studio8502/Sentinel-65X/kicad/Sentinel 65X - Prototype 3 Mini/Sentinel 65X - Prototype 3 Mini.kicad_sch

## KiCad design kicad/Sentinel 65X - Prototype 3 Mini/Sentinel 65X - Prototype 3 Mini.kicad_sch (2024-02-07)

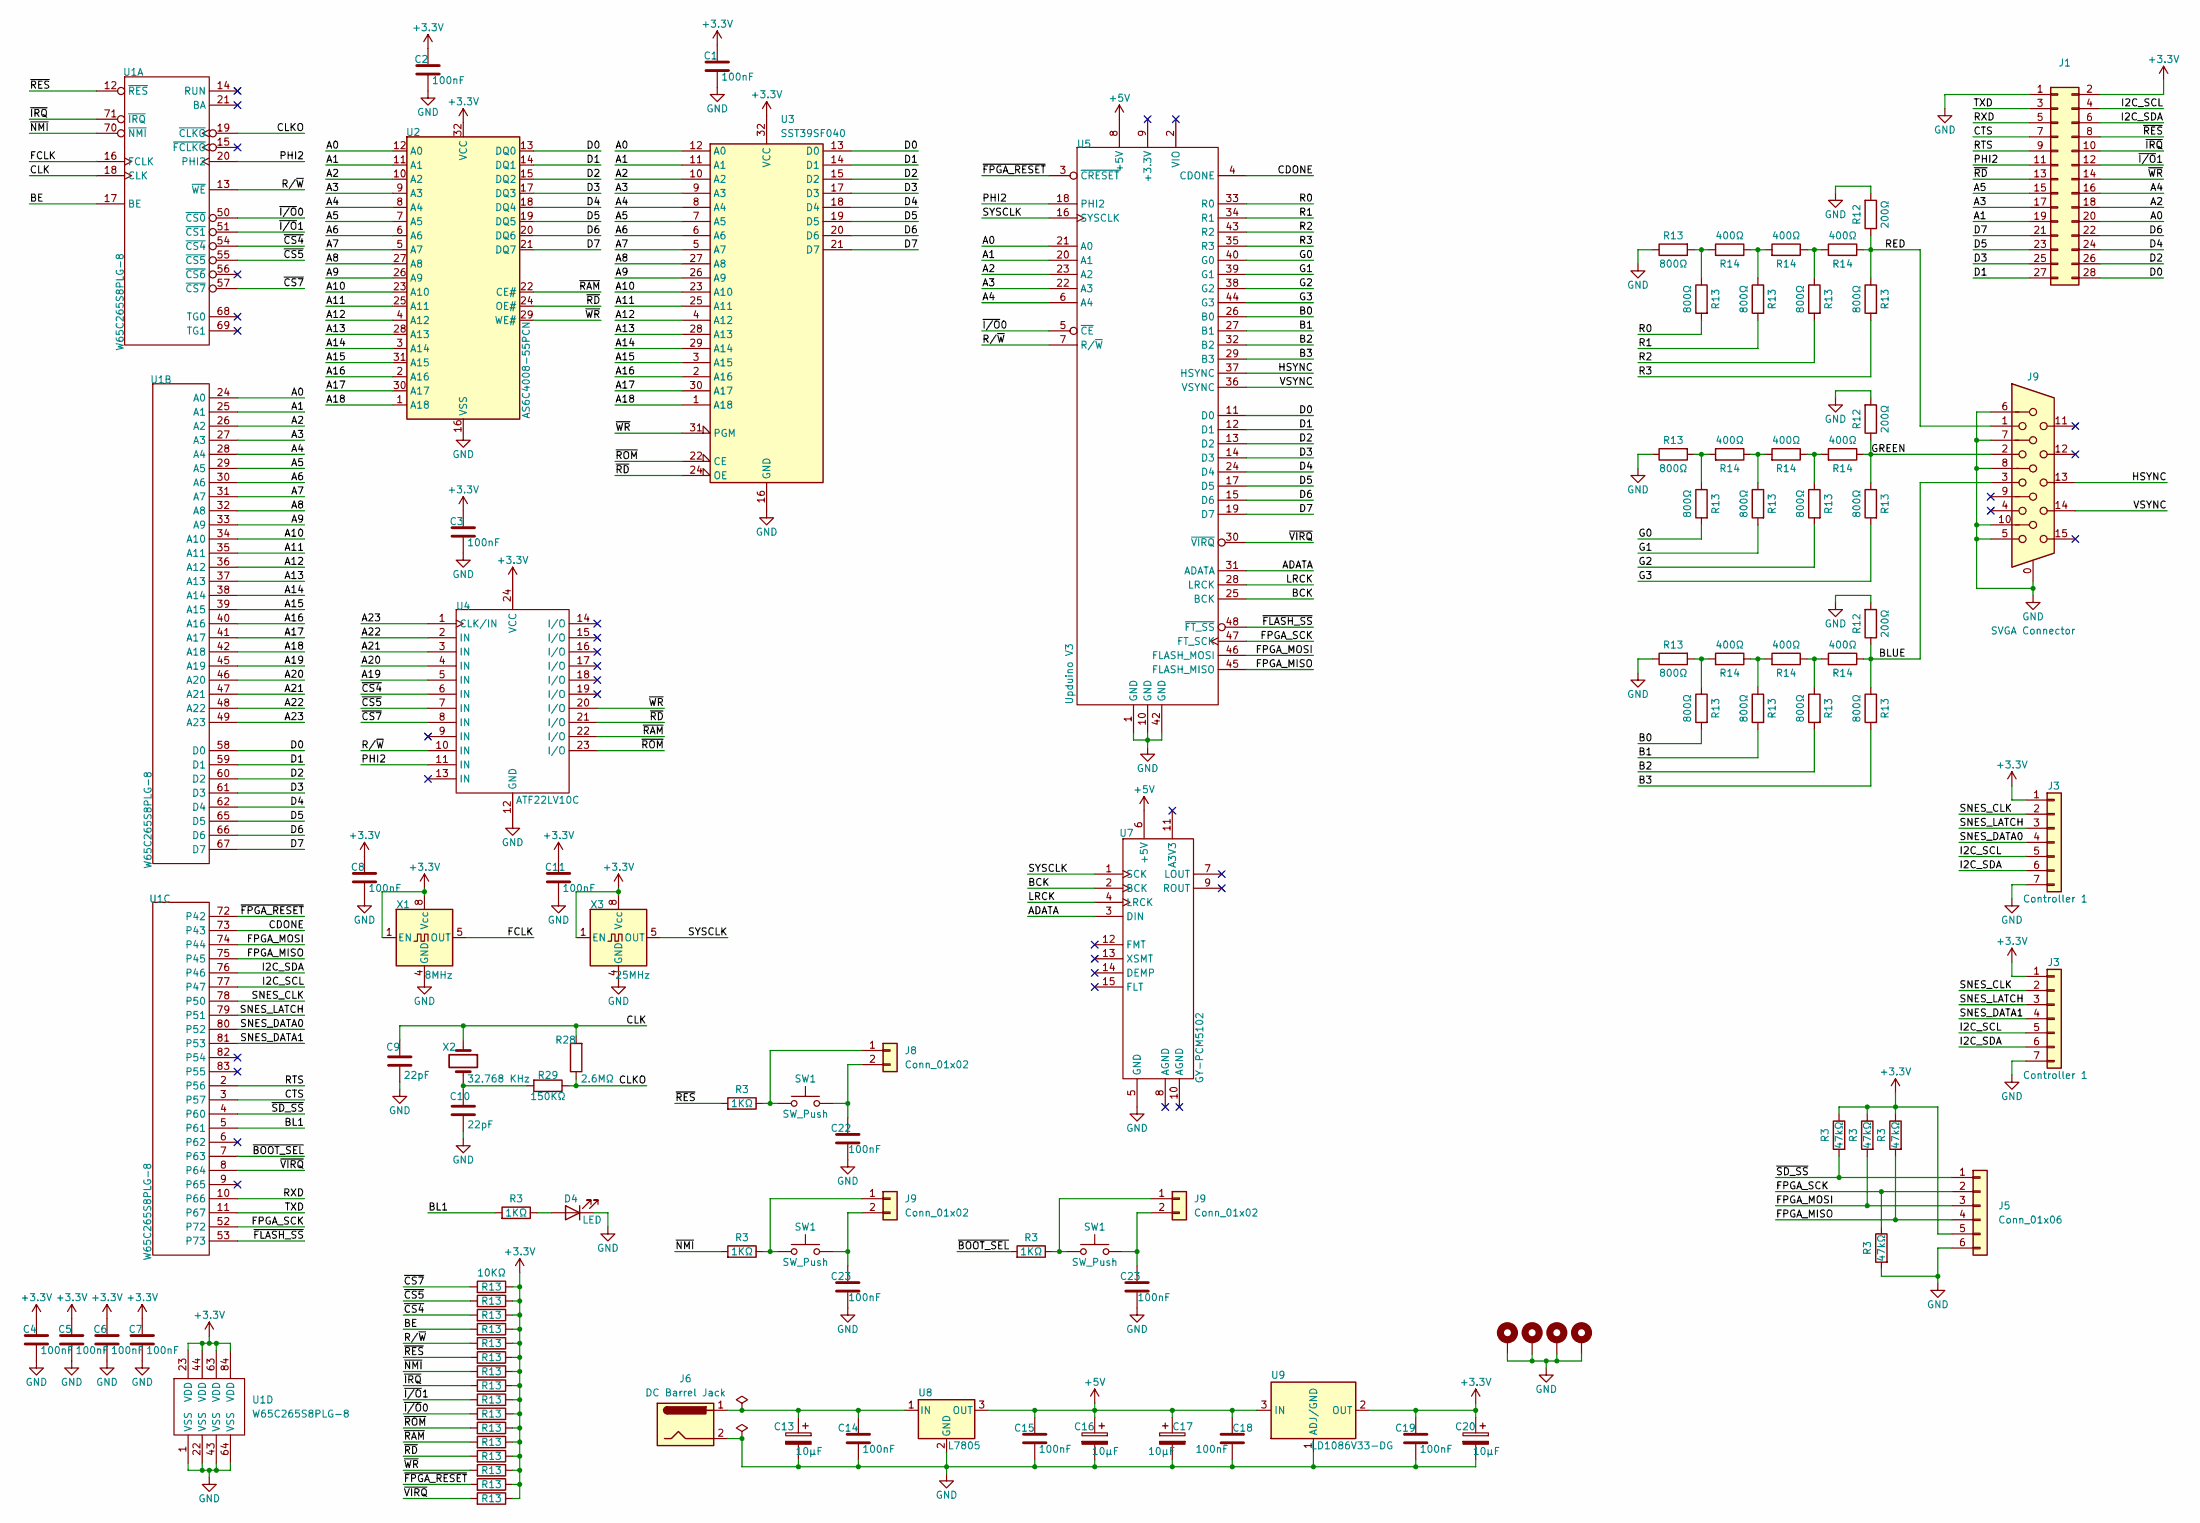
[picture p14: schematic Sentinel 65X - Prototype 3 Mini.kicad_sch]

Parts:
C1, C2, C3, C4, C5, C6, C7, C8, C11, C14, C15, C18, C19, C22, C23: 100nF; C_Disc_D3.4mm_W2.1mm_P2.50mm
C9, C10: 22pF; C_Disc_D3.0mm_W1.6mm_P2.50mm
C13, C16, C17, C20: 10µF; CP_Radial_D5.0mm_P2.50mm
D4: LED; LED_D3.0mm
H1, H2, H3, H4: MountingHole_Pad; MountingHole_3.2mm_M3_DIN965_Pad
J1: Conn_02x14_Odd_Even; PinSocket_2x14_P2.54mm_Vertical
J3: Controller 1; SNES Controller Port (Female, 90º, THT)
J5: Conn_01x06; PinSocket_1x06_P2.54mm_Horizontal
J6: DC Barrel Jack; BarrelJack_Horizontal
J8: Conn_01x02; PinHeader_1x02_P2.54mm_Vertical
J9: SVGA Connector; DSUB-15-HD_Female_Horizontal_P2.29x1.98mm_EdgePinOffset3.03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
R3: 1KΩ; R_Axial_DIN0204_L3.6mm_D1.6mm_P5.08mm_Horizontal
R12: 200Ω; R_Axial_DIN0204_L3.6mm_D1.6mm_P5.08mm_Horizontal
R13: 10KΩ; R_Axial_DIN0204_L3.6mm_D1.6mm_P5.08mm_Horizontal
R14: 400Ω; R_Axial_DIN0204_L3.6mm_D1.6mm_P5.08mm_Horizontal
R28: 2.6MΩ; R_Axial_DIN0204_L3.6mm_D1.6mm_P5.08mm_Horizontal
R29: 150KΩ; R_Axial_DIN0204_L3.6mm_D1.6mm_P5.08mm_Horizontal
SW1: SW_Push; SW_Tactile_Straight_KSA0Axx1LFTR
U1: W65C265S8PLG-8; PLCC-84_THT-Socket
U2: AS6C4008-55PCN; DIP-32_W15.24mm_Socket_LongPads
U3: SST39SF040; DIP-32_W15.24mm_Socket_LongPads
U4: ATF22LV10C; DIP-24_W7.62mm_Socket_LongPads
U5: Upduino V3; DIP-48_W17.76mm_Socket_LongPads
U7: GY-PCM5102
U8: L7805; TO-220-3_Vertical
U9: LD1086V33-DG; TO-220-3_Vertical
X1: 8MHz; Oscillator_DIP-8
X2: 32.768 KHz; Crystal_DS10_D1.0mm_L4.3mm_Horizontal
X3: 25MHz; Oscillator_DIP-8

Connections:
+3.3V: C1.1, C2.1, C3.1, C4.1, C5.1, C6.1, C7.1, C8.1, C11.1, C19.1, C20.1, J1.2, J3.1, J5.5, R3.1, R13.1, U1.23 (VDD), U1.44 (VDD), U1.63 (VDD), U1.84 (VDD), U2.32 (VCC), U3.32 (VCC), U4.24 (VCC), U9.2 (OUT), X1.1 (EN), X1.8 (Vcc), X3.1 (EN), X3.8 (Vcc)
+5V: C15.1, C16.1, C17.1, C18.1, U5.8 (+5V), U7.6 (+5V), U8.3 (OUT), U9.3 (IN)
A0: J1.20, U1.24 (A0), U2.12 (A0), U3.12 (A0), U5.21 (A0)
A1: J1.19, U1.25 (A1), U2.11 (A1), U3.11 (A1), U5.20 (A1)
A2: J1.18, U1.26 (A2), U2.10 (A2), U3.10 (A2), U5.23 (A2)
A3: J1.17, U1.27 (A3), U2.9 (A3), U3.9 (A3), U5.22 (A3)
A4: J1.16, U1.28 (A4), U2.8 (A4), U3.8 (A4), U5.6 (A4)
A5: J1.15, U1.29 (A5), U2.7 (A5), U3.7 (A5)
A6: U1.30 (A6), U2.6 (A6), U3.6 (A6)
A7: U1.31 (A7), U2.5 (A7), U3.5 (A7)
A8: U1.32 (A8), U2.27 (A8), U3.27 (A8)
A9: U1.33 (A9), U2.26 (A9), U3.26 (A9)
A10: U1.34 (A10), U2.23 (A10), U3.23 (A10)
A11: U1.35 (A11), U2.25 (A11), U3.25 (A11)
A12: U1.36 (A12), U2.4 (A12), U3.4 (A12)
A13: U1.37 (A13), U2.28 (A13), U3.28 (A13)
A14: U1.38 (A14), U2.3 (A14), U3.29 (A14)
A15: U1.39 (A15), U2.31 (A15), U3.3 (A15)
A16: U1.40 (A16), U2.2 (A16), U3.2 (A16)
A17: U1.41 (A17), U2.30 (A17), U3.30 (A17)
A18: U1.42 (A18), U2.1 (A18), U3.1 (A18)
A19: U1.45 (A19), U4.5 (IN)
A20: U1.46 (A20), U4.4 (IN)
A21: U1.47 (A21), U4.3 (IN)
A22: U1.48 (A22), U4.2 (IN)
A23: U1.49 (A23), U4.1 (CLK/IN)
ADATA: U5.31 (ADATA), U7.3 (DIN)
B0: R13.2, U5.26 (B0)
B1: R13.2, U5.27 (B1)
B2: R13.2, U5.32 (B2)
B3: R13.2, U5.29 (B3)
BCK: U5.25 (BCK), U7.2 (BCK)
BE: R13.2, U1.17 (BE)
BL1: R3.2, U1.5 (P61)
BLUE: J9.3, R12.1, R13.1, R14.1
CDONE: U1.73 (P43), U5.4 (CDONE)
CLK: C9.1, R28.2, U1.18 (CLK), X2.1
CLKO: R28.1, R29.1, U1.19 (~CLKO)
CTS: J1.7, U1.3 (P57)
D0: J1.28, U1.58 (D0), U2.13 (DQ0), U3.13 (D0), U5.11 (D0)
D1: J1.27, U1.59 (D1), U2.14 (DQ1), U3.14 (D1), U5.12 (D1)
D2: J1.26, U1.60 (D2), U2.15 (DQ2), U3.15 (D2), U5.13 (D2)
D3: J1.25, U1.61 (D3), U2.17 (DQ3), U3.17 (D3), U5.14 (D3)
D4: J1.24, U1.62 (D4), U2.18 (DQ4), U3.18 (D4), U5.24 (D4)
D5: J1.23, U1.65 (D5), U2.19 (DQ5), U3.19 (D5), U5.17 (D5)
D6: J1.22, U1.66 (D6), U2.20 (DQ6), U3.20 (D6), U5.15 (D6)
D7: J1.21, U1.67 (D7), U2.21 (DQ7), U3.21 (D7), U5.19 (D7)
FCLK: U1.16 (FCLK), X1.5 (OUT)
FPGA_MISO: J5.4, R3.2, U1.75 (P45), U5.45 (FLASH_MISO)
FPGA_MOSI: J5.3, R3.2, U1.74 (P44), U5.46 (FLASH_MOSI)
FPGA_SCK: J5.2, R3.1, U1.52 (P72), U5.47 (FT_SCK)
G0: R13.2, U5.40 (G0)
G1: R13.2, U5.39 (G1)
G2: R13.2, U5.38 (G2)
G3: R13.2, U5.44 (G3)
GND: C1.2, C2.2, C3.2, C4.2, C5.2, C6.2, C7.2, C8.2, C9.2, C10.2, C11.2, C13.2, C14.2, C15.2, C16.2, C17.2, C18.2, C19.2, C20.2, C22.2, C23.2, D4.1 (K), H1.1, H2.1, H3.1, H4.1, J1.1, J3.7, J5.6, J6.2, J9.0, J9.5, J9.6, J9.7, J9.8, J9.10, R3.2, R12.2, R13.1, U1.1 (VSS), U1.22 (VSS), U1.43 (VSS), U1.64 (VSS), U2.16 (VSS), U3.16 (GND), U4.12 (GND), U5.1 (GND), U5.10 (GND), U5.42 (GND), U7.5 (GND), U8.2 (GND), U9.1 (ADJ/GND), X1.4 (GND), X3.4 (GND)
GREEN: J9.2, R12.1, R13.1, R14.1
HSYNC: J9.13, U5.37 (HSYNC)
I2C_SCL: J1.4, J3.5, U1.77 (P47)
I2C_SDA: J1.6, J3.6, U1.76 (P46)
LRCK: U5.28 (LRCK), U7.4 (LRCK)
unnamed: C10.1, R29.2, X2.2
unnamed: C13.1, C14.1, J6.1, U8.1 (IN)
unnamed: C22.1, J8.2, SW1.2
unnamed: C23.1, J9.2, SW1.2
unnamed: D4.2 (A), R3.1
unnamed: J8.1, R3.1, SW1.1
unnamed: J9.1, R3.1, SW1.1
unnamed: R13.1, R13.2, R14.1, R14.2
PHI2: J1.11, U1.20 (PHI2), U4.11 (IN), U5.18 (PHI2)
R0: R13.2, U5.33 (R0)
R1: R13.2, U5.34 (R1)
R2: R13.2, U5.43 (R2)
R3: R13.2, U5.35 (R3)
RED: J9.1, R12.1, R13.1, R14.1
RTS: J1.9, U1.2 (P56)
RXD: J1.5, U1.10 (P66)
R/~W: R13.2, U1.13 (~WE), U4.10 (IN), U5.7 (R/~W)
SNES_CLK: J3.2, U1.78 (P50)
SNES_DATA0: J3.4, U1.80 (P52)
SNES_DATA1: J3.4, U1.81 (P53)
SNES_LATCH: J3.3, U1.79 (P51)
SYSCLK: U5.16 (SYSCLK), U7.1 (SCK), X3.5 (OUT)
TXD: J1.3, U1.11 (P67)
VSYNC: J9.14, U5.36 (VSYNC)
~BOOT_SEL: R3.2, U1.7 (P63)
~CS4: R13.2, U1.54 (~CS4), U4.6 (IN)
~CS5: R13.2, U1.55 (~CS5), U4.7 (IN)
~CS7: R13.2, U1.57 (~CS7), U4.8 (IN)
~FLASH_SS: U1.53 (P73), U5.48 (~FT_SS)
~FPGA_RESET: R13.2, U1.72 (P42), U5.3 (~CRESET)
~IRQ: J1.10, R13.2, U1.71 (~IRQ)
~I/O0: R13.2, U1.50 (~CS0), U5.5 (~CE)
~I/O1: J1.12, R13.2, U1.51 (~CS1)
~NMI: R3.2, R13.2, U1.70 (~NMI)
~RAM: R13.2, U2.22 (CE#), U4.22 (I/O)
~RD: J1.13, R13.2, U2.24 (OE#), U3.24 (OE), U4.21 (I/O)
~RES: J1.8, R3.2, R13.2, U1.12 (~RES)
~ROM: R13.2, U3.22 (CE), U4.23 (I/O)
~SD_SS: J5.1, R3.2, U1.4 (P60)
~VIRQ: R13.2, U1.8 (P64), U5.30 (~VIRQ)
~WR: J1.14, R13.2, U2.29 (WE#), U3.31 (PGM), U4.20 (I/O)
