studio8502/Sentinel-65X/kicad/Sentinel 65X - Prototype 4 V2/AV Port.kicad_sch

## KiCad design kicad/Sentinel 65X - Prototype 4 V2/AV Port.kicad_sch (2024-03-17)

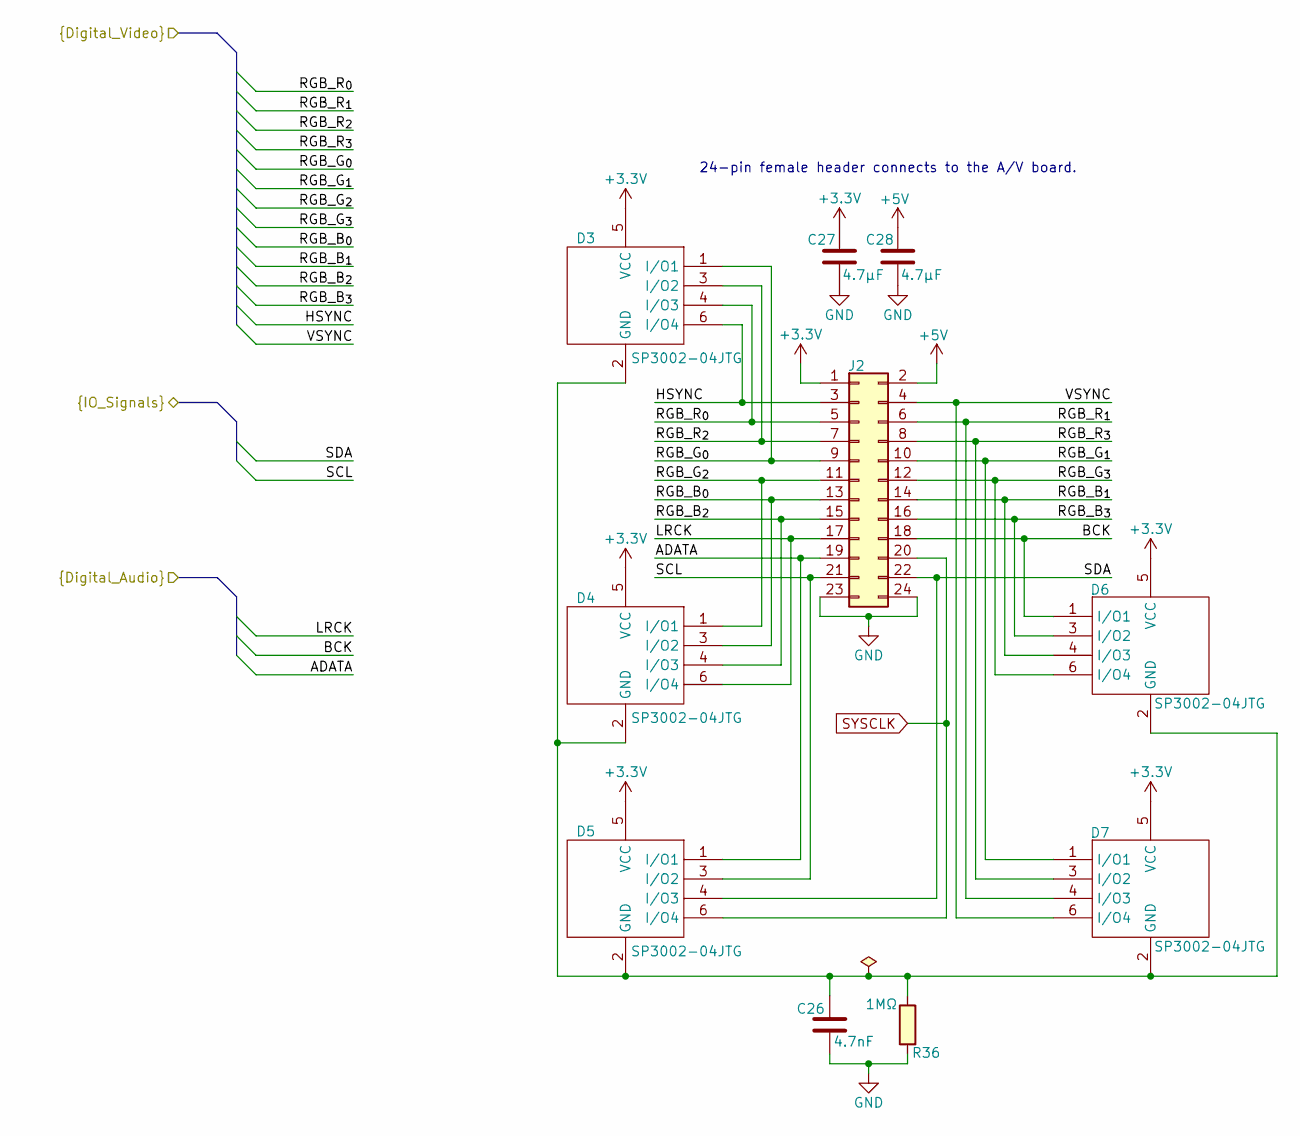
[picture p15: schematic AV Port.kicad_sch]

Parts:
C26: 4.7nF; C_0402_1005Metric
C27, C28: 4.7µF; C_0402_1005Metric
D3, D4, D5, D6, D7: SP3002-04JTG; SOT-363_SC-70-6
J2: Conn_02x12_Odd_Even; PinSocket_2x12_P2.54mm_Vertical
R36: 1MΩ; R_0402_1005Metric

Connections:
+3.3V: C27.1, D3.5 (VCC), D4.5 (VCC), D5.5 (VCC), D6.5 (VCC), D7.5 (VCC), J2.1
+5V: C28.1, J2.2
ADATA: D5.1 (I/O1), J2.19
BCK: D6.1 (I/O1), J2.18
GND: C26.1, C27.2, C28.2, J2.23, J2.24, R36.1
HSYNC: D3.6 (I/O4), J2.3
LRCK: D4.6 (I/O4), J2.17
unnamed: C26.2, D3.2 (GND), D4.2 (GND), D5.2 (GND), D6.2 (GND), D7.2 (GND), R36.2
RGB_B_{0}: D4.3 (I/O2), J2.13
RGB_B_{1}: D6.4 (I/O3), J2.14
RGB_B_{2}: D4.4 (I/O3), J2.15
RGB_B_{3}: D6.3 (I/O2), J2.16
RGB_G_{0}: D3.1 (I/O1), J2.9
RGB_G_{1}: D7.1 (I/O1), J2.10
RGB_G_{2}: D4.1 (I/O1), J2.11
RGB_G_{3}: D6.6 (I/O4), J2.12
RGB_R_{0}: D3.4 (I/O3), J2.5
RGB_R_{1}: D7.4 (I/O3), J2.6
RGB_R_{2}: D3.3 (I/O2), J2.7
RGB_R_{3}: D7.3 (I/O2), J2.8
SCL: D5.3 (I/O2), J2.21
SDA: D5.4 (I/O3), J2.22
SYSCLK: D5.6 (I/O4), J2.20
VSYNC: D7.6 (I/O4), J2.4

Notes on the sheet:
24-pin female header connects to the A/V board.
