studio8502/Sentinel-65X/kicad/Sentinel 65X - Prototype 4 V2/Cartridge Port.kicad_sch

## KiCad design kicad/Sentinel 65X - Prototype 4 V2/Cartridge Port.kicad_sch (2024-03-17)

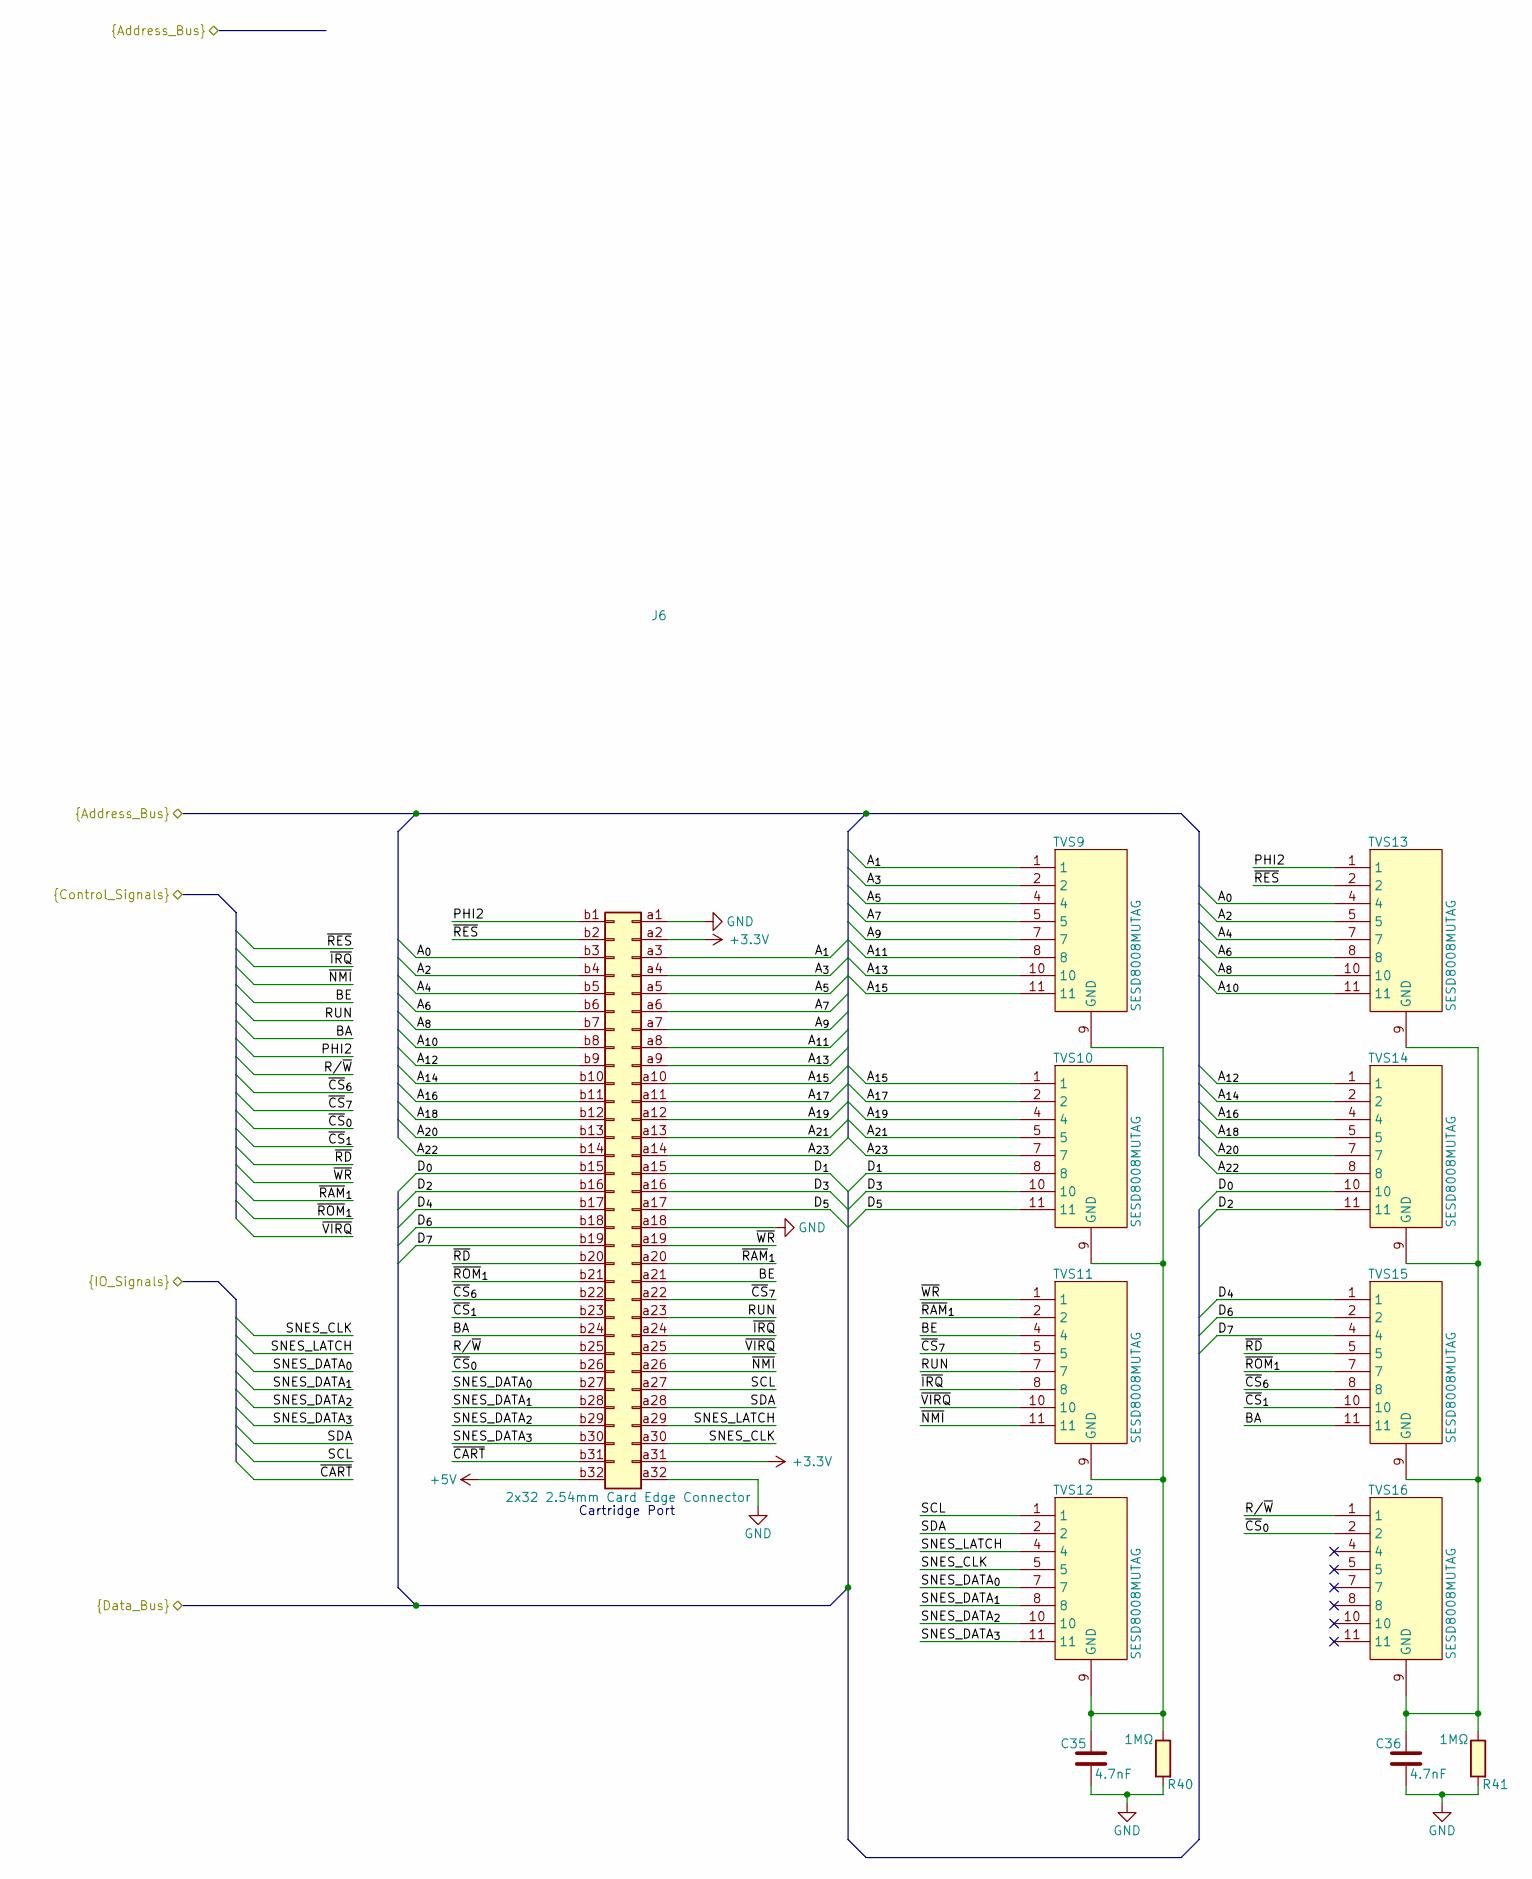
[picture p16: schematic Cartridge Port.kicad_sch]

Parts:
C35, C36: 4.7nF; C_0402_1005Metric
J6: 2x32 2.54mm Card Edge Connector; Sentinel 65X Cartridge Port
R40, R41: 1MΩ; R_0402_1005Metric
TVS9, TVS10, TVS11, TVS12, TVS13, TVS14, TVS15, TVS16: SESD8008MUTAG

Connections:
+3.3V: J6.a2, J6.a31
+5V: J6.b32
A_{0}: J6.b3, TVS13.4
A_{1}: J6.a3, TVS9.1
A_{2}: J6.b4, TVS13.5
A_{3}: J6.a4, TVS9.2
A_{4}: J6.b5, TVS13.7
A_{5}: J6.a5, TVS9.4
A_{6}: J6.b6, TVS13.8
A_{7}: J6.a6, TVS9.5
A_{8}: J6.b7, TVS13.10
A_{9}: J6.a7, TVS9.7
A_{10}: J6.b8, TVS13.11
A_{11}: J6.a8, TVS9.8
A_{12}: J6.b9, TVS14.1
A_{13}: J6.a9, TVS9.10
A_{14}: J6.b10, TVS14.2
A_{15}: J6.a10, TVS9.11, TVS10.1
A_{16}: J6.b11, TVS14.4
A_{17}: J6.a11, TVS10.2
A_{18}: J6.b12, TVS14.5
A_{19}: J6.a12, TVS10.4
A_{20}: J6.b13, TVS14.7
A_{21}: J6.a13, TVS10.5
A_{22}: J6.b14, TVS14.8
A_{23}: J6.a14, TVS10.7
BA: J6.b24, TVS15.11
BE: J6.a21, TVS11.4
D_{0}: J6.b15, TVS14.10
D_{1}: J6.a15, TVS10.8
D_{2}: J6.b16, TVS14.11
D_{3}: J6.a16, TVS10.10
D_{4}: J6.b17, TVS15.1
D_{5}: J6.a17, TVS10.11
D_{6}: J6.b18, TVS15.2
D_{7}: J6.b19, TVS15.4
GND: C35.1, C36.1, J6.a1, J6.a18, J6.a32, R40.1, R41.1
unnamed: C35.2, R40.2, TVS9.3 (GND), TVS9.6 (GND), TVS9.9 (GND), TVS9.12 (GND), TVS9.13 (GND), TVS9.14 (GND), TVS10.3 (GND), TVS10.6 (GND), TVS10.9 (GND), TVS10.12 (GND), TVS10.13 (GND), TVS10.14 (GND), TVS11.3 (GND), TVS11.6 (GND), TVS11.9 (GND), TVS11.12 (GND), TVS11.13 (GND), TVS11.14 (GND), TVS12.3 (GND), TVS12.6 (GND), TVS12.9 (GND), TVS12.12 (GND), TVS12.13 (GND), TVS12.14 (GND)
unnamed: C36.2, R41.2, TVS13.3 (GND), TVS13.6 (GND), TVS13.9 (GND), TVS13.12 (GND), TVS13.13 (GND), TVS13.14 (GND), TVS14.3 (GND), TVS14.6 (GND), TVS14.9 (GND), TVS14.12 (GND), TVS14.13 (GND), TVS14.14 (GND), TVS15.3 (GND), TVS15.6 (GND), TVS15.9 (GND), TVS15.12 (GND), TVS15.13 (GND), TVS15.14 (GND), TVS16.3 (GND), TVS16.6 (GND), TVS16.9 (GND), TVS16.12 (GND), TVS16.13 (GND), TVS16.14 (GND)
PHI2: J6.b1, TVS13.1
RUN: J6.a23, TVS11.7
R/~W: J6.b25, TVS16.1
SCL: J6.a27, TVS12.1
SDA: J6.a28, TVS12.2
SNES_CLK: J6.a30, TVS12.5
SNES_DATA_{0}: J6.b27, TVS12.7
SNES_DATA_{1}: J6.b28, TVS12.8
SNES_DATA_{2}: J6.b29, TVS12.10
SNES_DATA_{3}: J6.b30, TVS12.11
SNES_LATCH: J6.a29, TVS12.4
~CART: J6.b31
~CS_{0}: J6.b26, TVS16.2
~CS_{1}: J6.b23, TVS15.10
~CS_{6}: J6.b22, TVS15.8
~CS_{7}: J6.a22, TVS11.5
~IRQ: J6.a24, TVS11.8
~NMI: J6.a26, TVS11.11
~RAM_{1}: J6.a20, TVS11.2
~RD: J6.b20, TVS15.5
~RES: J6.b2, TVS13.2
~ROM_{1}: J6.b21, TVS15.7
~VIRQ: J6.a25, TVS11.10
~WR: J6.a19, TVS11.1

Notes on the sheet:
Cartridge Port
