studio8502/Sentinel-65X/kicad/Sentinel 65X - Prototype 4 V2/Expansion Ports.kicad_sch

## KiCad design kicad/Sentinel 65X - Prototype 4 V2/Expansion Ports.kicad_sch (2024-03-17)

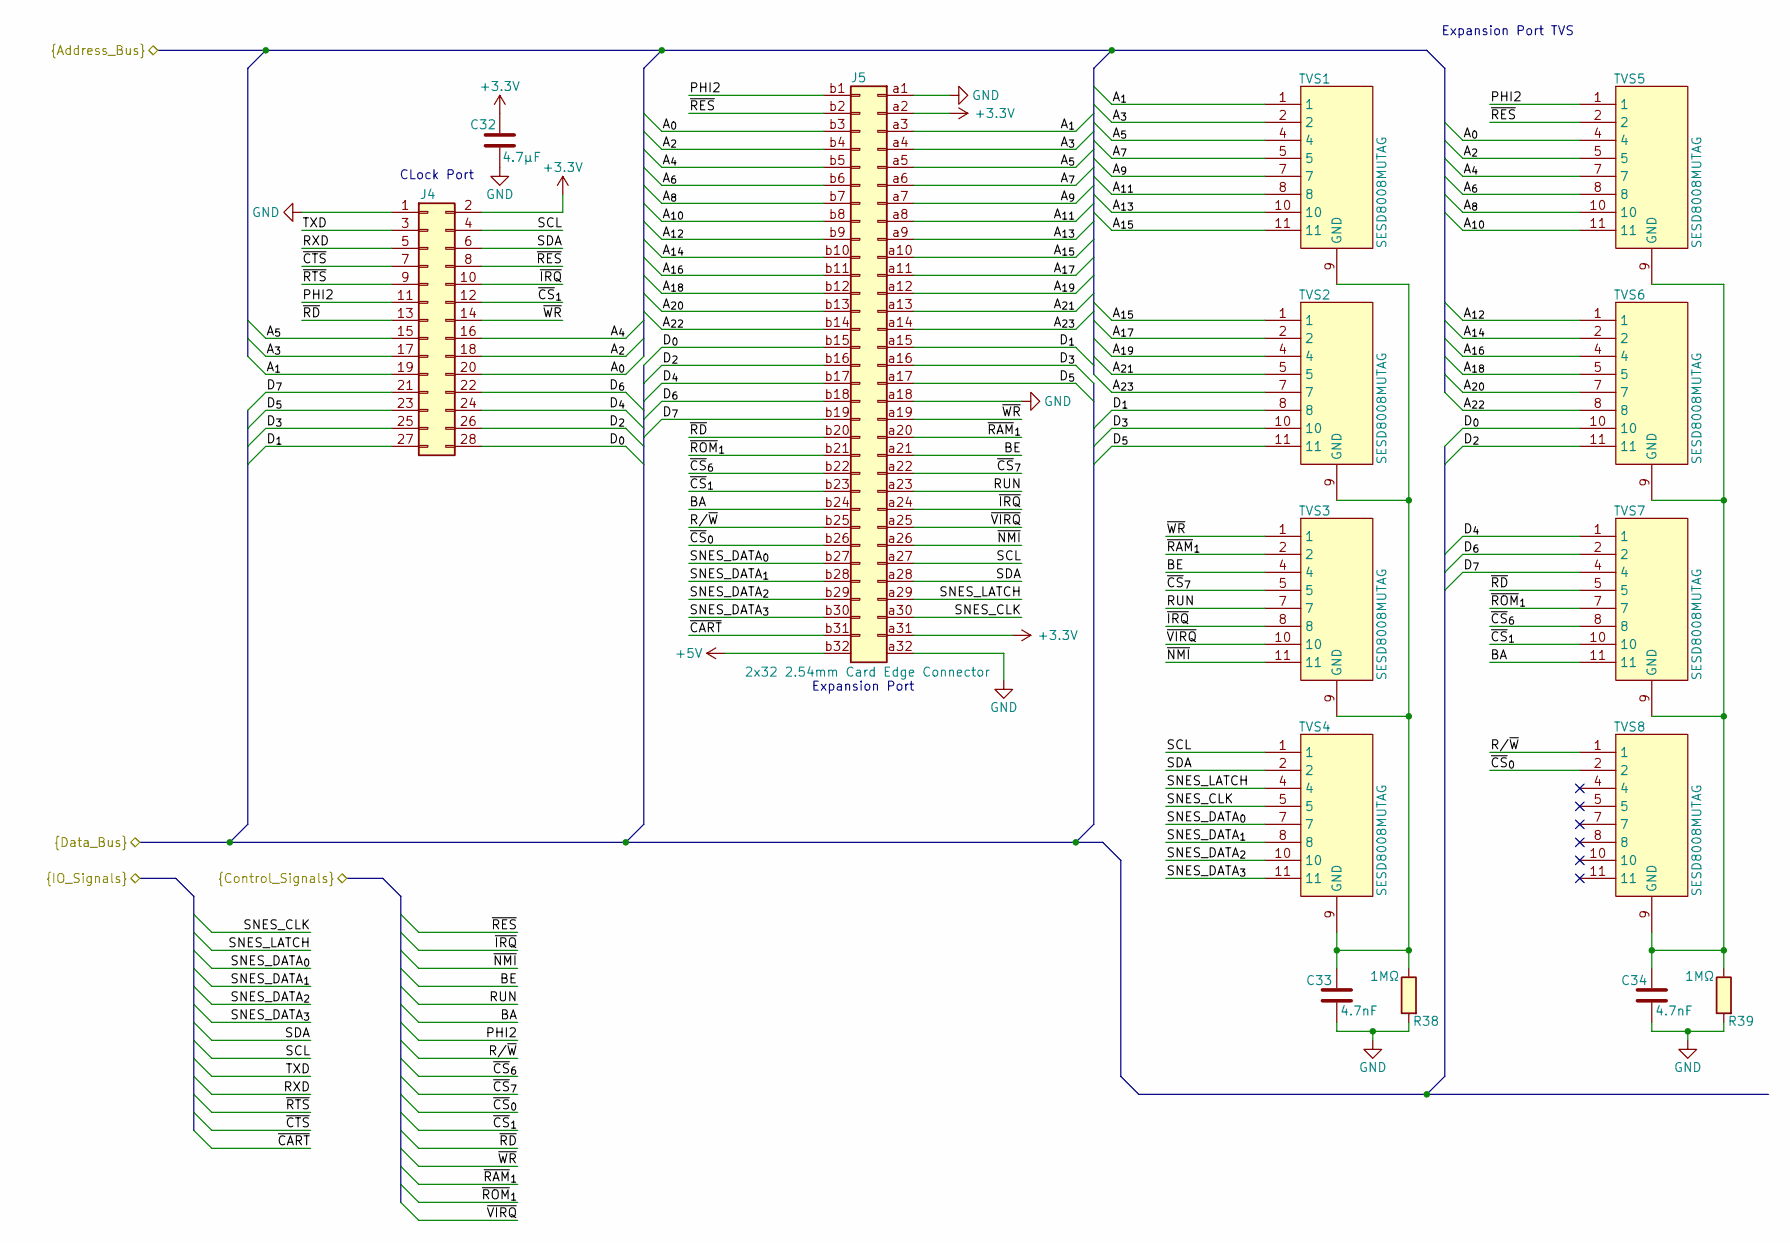
[picture p17: schematic Expansion Ports.kicad_sch]

Parts:
C32: 4.7µF; C_0402_1005Metric
C33, C34: 4.7nF; C_0402_1005Metric
J4: Conn_02x14_Odd_Even; PinSocket_2x14_P2.54mm_Vertical
J5: 2x32 2.54mm Card Edge Connector; Sentinel 65X Expansion Port
R38, R39: 1MΩ; R_0402_1005Metric
TVS1, TVS2, TVS3, TVS4, TVS5, TVS6, TVS7, TVS8: SESD8008MUTAG

Connections:
+3.3V: C32.1, J4.2, J5.a2, J5.a31
+5V: J5.b32
A_{0}: J4.20, J5.b3, TVS5.4
A_{1}: J4.19, J5.a3, TVS1.1
A_{2}: J4.18, J5.b4, TVS5.5
A_{3}: J4.17, J5.a4, TVS1.2
A_{4}: J4.16, J5.b5, TVS5.7
A_{5}: J4.15, J5.a5, TVS1.4
A_{6}: J5.b6, TVS5.8
A_{7}: J5.a6, TVS1.5
A_{8}: J5.b7, TVS5.10
A_{9}: J5.a7, TVS1.7
A_{10}: J5.b8, TVS5.11
A_{11}: J5.a8, TVS1.8
A_{12}: J5.b9, TVS6.1
A_{13}: J5.a9, TVS1.10
A_{14}: J5.b10, TVS6.2
A_{15}: J5.a10, TVS1.11, TVS2.1
A_{16}: J5.b11, TVS6.4
A_{17}: J5.a11, TVS2.2
A_{18}: J5.b12, TVS6.5
A_{19}: J5.a12, TVS2.4
A_{20}: J5.b13, TVS6.7
A_{21}: J5.a13, TVS2.5
A_{22}: J5.b14, TVS6.8
A_{23}: J5.a14, TVS2.7
BA: J5.b24, TVS7.11
BE: J5.a21, TVS3.4
D_{0}: J4.28, J5.b15, TVS6.10
D_{1}: J4.27, J5.a15, TVS2.8
D_{2}: J4.26, J5.b16, TVS6.11
D_{3}: J4.25, J5.a16, TVS2.10
D_{4}: J4.24, J5.b17, TVS7.1
D_{5}: J4.23, J5.a17, TVS2.11
D_{6}: J4.22, J5.b18, TVS7.2
D_{7}: J4.21, J5.b19, TVS7.4
GND: C32.2, C33.1, C34.1, J4.1, J5.a1, J5.a18, J5.a32, R38.1, R39.1
unnamed: C33.2, R38.2, TVS1.3 (GND), TVS1.6 (GND), TVS1.9 (GND), TVS1.12 (GND), TVS1.13 (GND), TVS1.14 (GND), TVS2.3 (GND), TVS2.6 (GND), TVS2.9 (GND), TVS2.12 (GND), TVS2.13 (GND), TVS2.14 (GND), TVS3.3 (GND), TVS3.6 (GND), TVS3.9 (GND), TVS3.12 (GND), TVS3.13 (GND), TVS3.14 (GND), TVS4.3 (GND), TVS4.6 (GND), TVS4.9 (GND), TVS4.12 (GND), TVS4.13 (GND), TVS4.14 (GND)
unnamed: C34.2, R39.2, TVS5.3 (GND), TVS5.6 (GND), TVS5.9 (GND), TVS5.12 (GND), TVS5.13 (GND), TVS5.14 (GND), TVS6.3 (GND), TVS6.6 (GND), TVS6.9 (GND), TVS6.12 (GND), TVS6.13 (GND), TVS6.14 (GND), TVS7.3 (GND), TVS7.6 (GND), TVS7.9 (GND), TVS7.12 (GND), TVS7.13 (GND), TVS7.14 (GND), TVS8.3 (GND), TVS8.6 (GND), TVS8.9 (GND), TVS8.12 (GND), TVS8.13 (GND), TVS8.14 (GND)
PHI2: J4.11, J5.b1, TVS5.1
RUN: J5.a23, TVS3.7
RXD: J4.5
R/~W: J5.b25, TVS8.1
SCL: J4.4, J5.a27, TVS4.1
SDA: J4.6, J5.a28, TVS4.2
SNES_CLK: J5.a30, TVS4.5
SNES_DATA_{0}: J5.b27, TVS4.7
SNES_DATA_{1}: J5.b28, TVS4.8
SNES_DATA_{2}: J5.b29, TVS4.10
SNES_DATA_{3}: J5.b30, TVS4.11
SNES_LATCH: J5.a29, TVS4.4
TXD: J4.3
~CART: J5.b31
~CS_{0}: J5.b26, TVS8.2
~CS_{1}: J4.12, J5.b23, TVS7.10
~CS_{6}: J5.b22, TVS7.8
~CS_{7}: J5.a22, TVS3.5
~CTS: J4.7
~IRQ: J4.10, J5.a24, TVS3.8
~NMI: J5.a26, TVS3.11
~RAM_{1}: J5.a20, TVS3.2
~RD: J4.13, J5.b20, TVS7.5
~RES: J4.8, J5.b2, TVS5.2
~ROM_{1}: J5.b21, TVS7.7
~RTS: J4.9
~VIRQ: J5.a25, TVS3.10
~WR: J4.14, J5.a19, TVS3.1

Notes on the sheet:
CLock Port
Expansion Port
Expansion Port TVS
