studio8502/Sentinel-65X/kicad/Sentinel 65X - Prototype 4 V2/Glue Logic.kicad_sch

## KiCad design kicad/Sentinel 65X - Prototype 4 V2/Glue Logic.kicad_sch (2024-03-17)

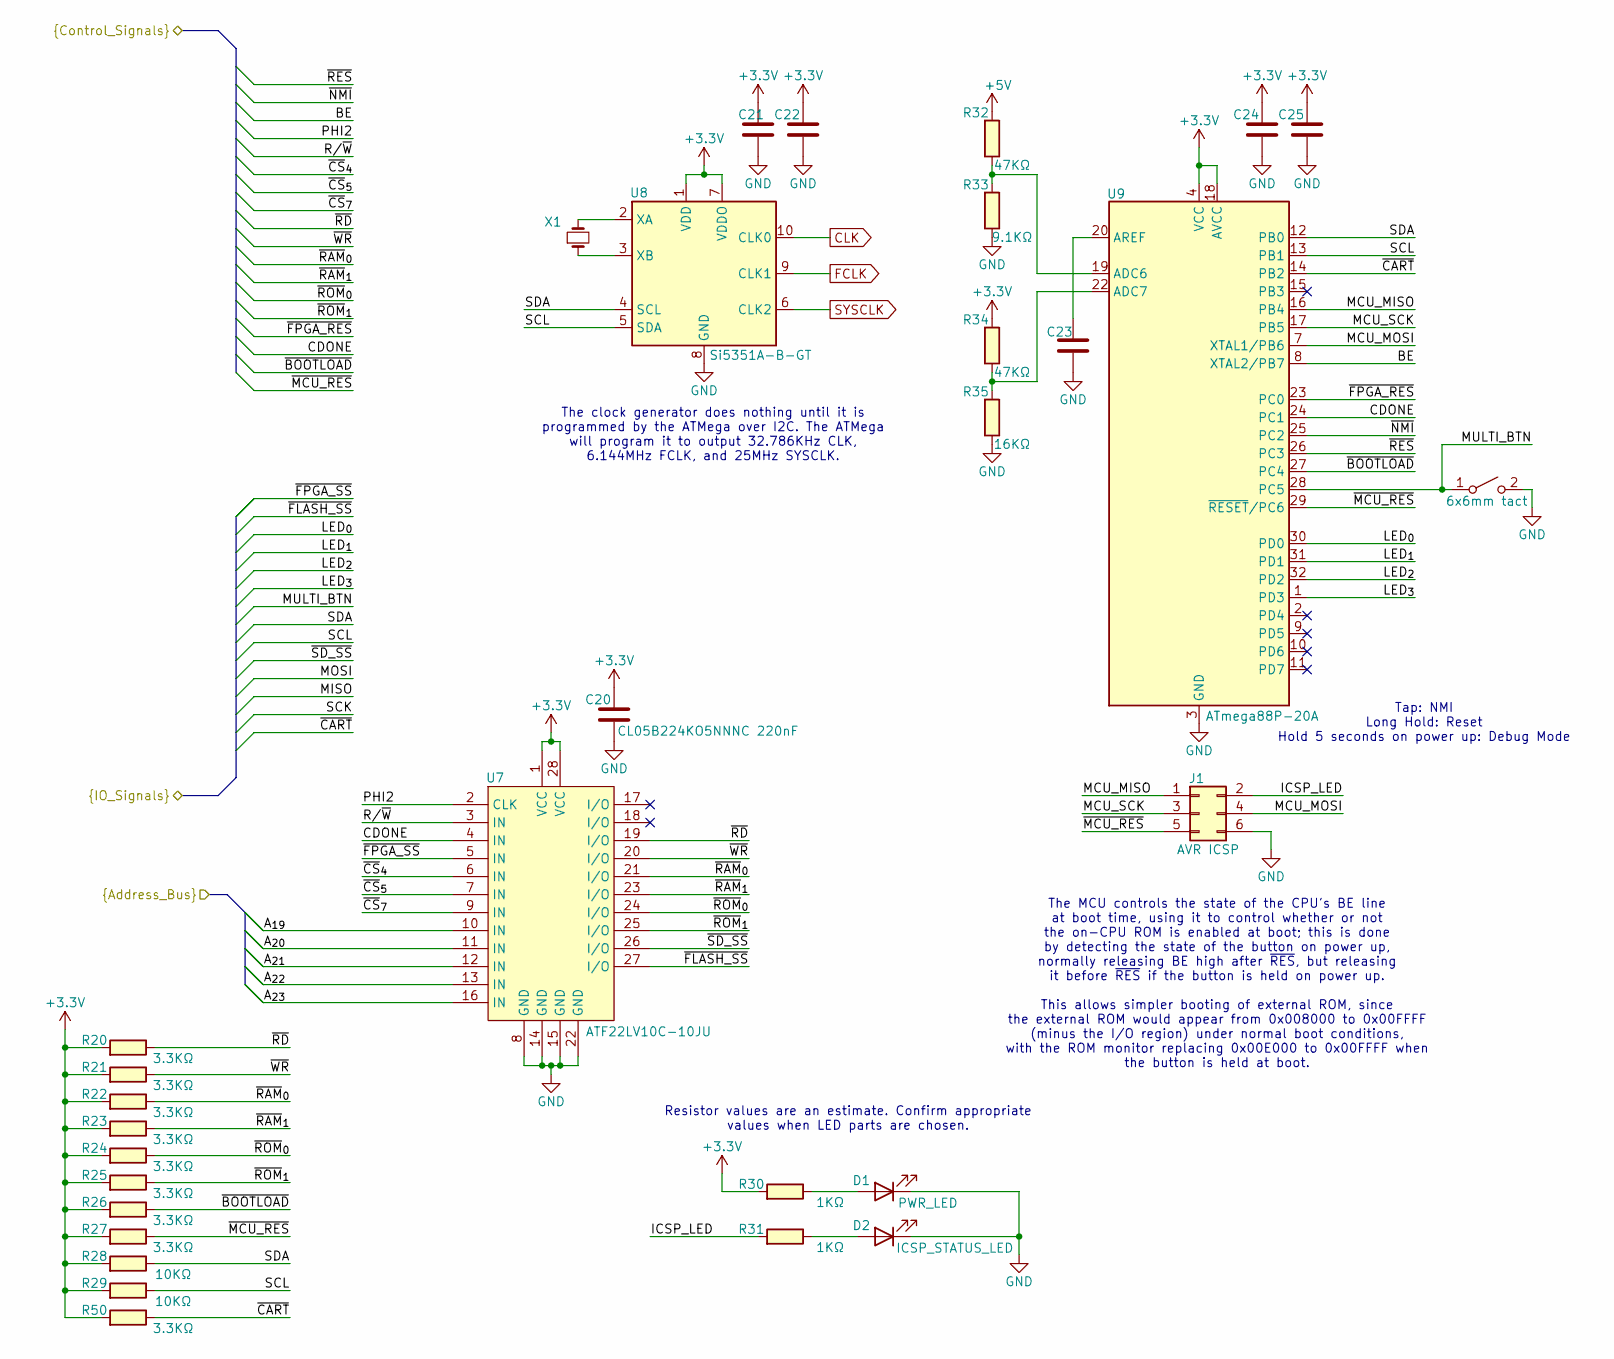
[picture p18: schematic Glue Logic.kicad_sch]

Parts:
C20: CL05B224KO5NNNC 220nF; C_0402_1005Metric
C21, C22, C23, C24, C25: CL05A106MQ5NUNC; C_0402_1005Metric
D1: PWR_LED; LED_D3.0mm
D2: ICSP_STATUS_LED; LED_D3.0mm
J1: AVR ICSP; PinHeader_2x03_P2.54mm_Vertical_SMD
R20, R21, R22, R23, R24, R25, R26, R27, R50: 3.3KΩ; R_0402_1005Metric
R28, R29: 10KΩ; R_0402_1005Metric
R30, R31: 1KΩ; R_0402_1005Metric
R32, R34: 47KΩ; R_0402_1005Metric
R33: 9.1KΩ; R_0402_1005Metric
R35: 16KΩ; R_0402_1005Metric
SW1: 6x6mm tact; SW_Push_1P1T_NO_6x6mm_H9.5mm
U7: ATF22LV10C-10JU; PLCC-28_SMD-Socket
U8: Si5351A-B-GT; MSOP-10_3x3mm_P0.5mm
U9: ATmega88P-20A; TQFP-32_7x7mm_P0.8mm
X1: ECS-250-6-37B2-AGY-TR; Crystal_SMD_2016-4Pin_2.0x1.6mm

Connections:
+3.3V: C20.1, C21.1, C22.1, C24.1, C25.1, R20.1, R21.1, R22.1, R23.1, R24.1, R25.1, R26.1, R27.1, R28.1, R29.1, R30.1, R34.1, R50.1, U7.1 (VCC), U7.28 (VCC), U8.1 (VDD), U8.7 (VDDO), U9.4 (VCC), U9.6 (VCC), U9.18 (AVCC)
+5V: R32.1
A_{19}: U7.10 (IN)
A_{20}: U7.11 (IN)
A_{21}: U7.12 (IN)
A_{22}: U7.13 (IN)
A_{23}: U7.16 (IN)
BE: U9.8 (XTAL2/PB7)
CDONE: U7.4 (IN), U9.24 (PC1)
CLK: U8.10 (CLK0)
FCLK: U8.9 (CLK1)
GND: C20.2, C21.2, C22.2, C23.2, C24.2, C25.2, D1.1 (K), D2.1 (K), J1.6, R33.2, R35.2, SW1.2 (B), U7.8 (GND), U7.14 (GND), U7.15 (GND), U7.22 (GND), U8.8 (GND), U9.3 (GND), U9.5 (GND), U9.21 (GND)
ICSP_LED: J1.2, R31.1
LED_{0}: U9.30 (PD0)
LED_{1}: U9.31 (PD1)
LED_{2}: U9.32 (PD2)
LED_{3}: U9.1 (PD3)
MCU_MISO: J1.1, U9.16 (PB4)
MCU_MOSI: J1.4, U9.7 (XTAL1/PB6)
MCU_SCK: J1.3, U9.17 (PB5)
MULTI_BTN: SW1.1 (A), U9.28 (PC5)
unnamed: C23.1, U9.20 (AREF)
unnamed: D1.2 (A), R30.2
unnamed: D2.2 (A), R31.2
unnamed: R32.2, R33.1, U9.19 (ADC6)
unnamed: R34.2, R35.1, U9.22 (ADC7)
unnamed: U8.2 (XA), X1.2
unnamed: U8.3 (XB), X1.1
PHI2: U7.2 (IN)
R/~W: U7.3 (IN)
SCL: R29.2, U8.5 (SDA), U9.13 (PB1)
SDA: R28.2, U8.4 (SCL), U9.12 (PB0)
SYSCLK: U8.6 (CLK2)
~BOOTLOAD: R26.2, U9.27 (PC4)
~CART: R50.2, U9.14 (PB2)
~CS_{4}: U7.6 (IN)
~CS_{5}: U7.7 (IN)
~CS_{7}: U7.9 (IN)
~FLASH_SS: U7.27 (I/O)
~FPGA_RES: U9.23 (PC0)
~FPGA_SS: U7.5 (IN)
~MCU_RES: J1.5, R27.2, U9.29 (~RESET/PC6)
~NMI: U9.25 (PC2)
~RAM_{0}: R22.2, U7.21 (I/O)
~RAM_{1}: R23.2, U7.23 (I/O)
~RD: R20.2, U7.19 (I/O)
~RES: U9.26 (PC3)
~ROM_{0}: R24.2, U7.24 (I/O)
~ROM_{1}: R25.2, U7.25 (I/O)
~SD_SS: U7.26 (I/O)
~WR: R21.2, U7.20 (I/O)

Notes on the sheet:
Tap: NMI Long Hold: Reset Hold 5 seconds on power up: Debug Mode
The MCU controls the state of the CPU's BE line at boot time, using it to control whether or not the on-CPU ROM is enabled at boot; this is done by detecting the state of the button on power up, normally releasing BE high after ~{RES}, but releasing it before ~{RES} if the button is held on power u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
The clock generator does nothing until it is programmed by the ATMega over I2C. The ATMega will program it to output 32.786KHz CLK, 6.144MHz FCLK, and 25MHz SYSCLK.
Resistor values are an estimate. Confirm appropriate values when LED parts are chosen.
