studio8502/Sentinel-65X/kicad/Sentinel 65X - Prototype 4 V2/IO Port.kicad_sch

## KiCad design kicad/Sentinel 65X - Prototype 4 V2/IO Port.kicad_sch (2024-03-15)

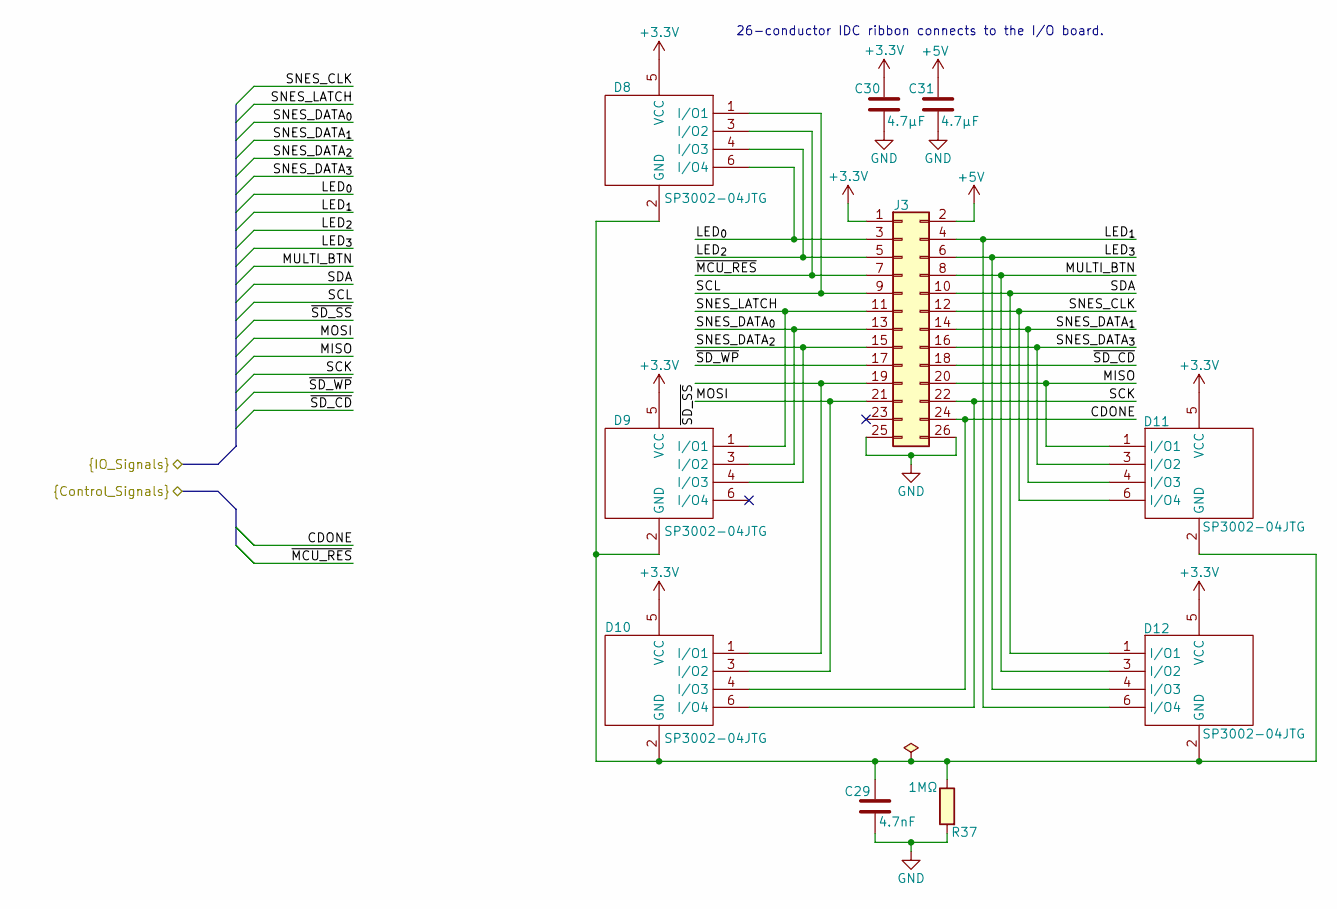
[picture p19: schematic IO Port.kicad_sch]

Parts:
C29: 4.7nF; C_0402_1005Metric
C30, C31: 4.7µF; C_0402_1005Metric
D8, D9, D10, D11, D12: SP3002-04JTG; SOT-363_SC-70-6
J3: Conn_02x13_Odd_Even; IDC-Header_2x13_P2.54mm_Vertical
R37: 1MΩ; R_0402_1005Metric

Connections:
+3.3V: C30.1, D8.5 (VCC), D9.5 (VCC), D10.5 (VCC), D11.5 (VCC), D12.5 (VCC), J3.1
+5V: C31.1, J3.2
CDONE: D10.4 (I/O3), J3.24
GND: C29.1, C30.2, C31.2, J3.25, J3.26, R37.1
LED_{0}: D8.6 (I/O4), J3.3
LED_{1}: D12.6 (I/O4), J3.4
LED_{2}: D8.4 (I/O3), J3.5
LED_{3}: D12.4 (I/O3), J3.6
MISO: D11.1 (I/O1), J3.20
MOSI: D10.3 (I/O2), J3.21
MULTI_BTN: D12.3 (I/O2), J3.8
unnamed: C29.2, D8.2 (GND), D9.2 (GND), D10.2 (GND), D11.2 (GND), D12.2 (GND), R37.2
SCK: D10.6 (I/O4), J3.22
SCL: D8.1 (I/O1), J3.9
SDA: D12.1 (I/O1), J3.10
SNES_CLK: D11.6 (I/O4), J3.12
SNES_DATA_{0}: D9.3 (I/O2), J3.13
SNES_DATA_{1}: D11.4 (I/O3), J3.14
SNES_DATA_{2}: D9.4 (I/O3), J3.15
SNES_DATA_{3}: D11.3 (I/O2), J3.16
SNES_LATCH: D9.1 (I/O1), J3.11
~MCU_RES: D8.3 (I/O2), J3.7
~SD_CD: J3.18
~SD_SS: D10.1 (I/O1), J3.19
~SD_WP: J3.17

Notes on the sheet:
26-conductor IDC ribbon connects to the I/O board.
