studio8502/Sentinel-65X/kicad/Sentinel 65X - Prototype 4 V2/Power Supply.kicad_sch

## KiCad design kicad/Sentinel 65X - Prototype 4 V2/Power Supply.kicad_sch (2024-03-17)

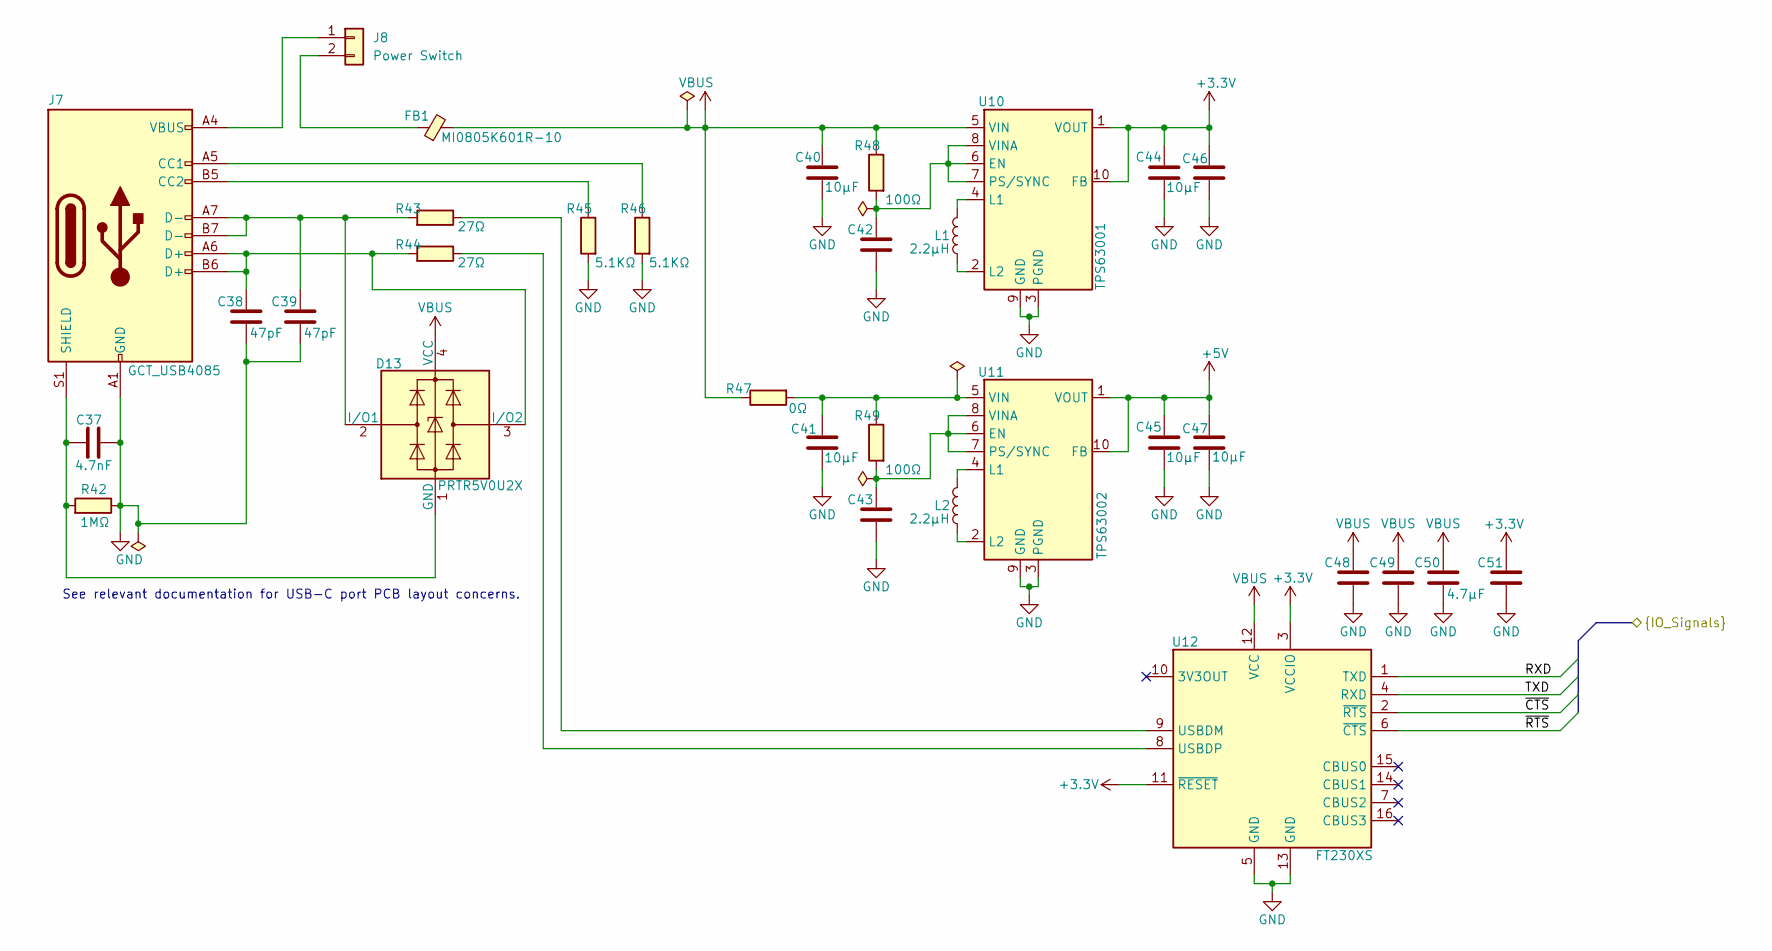
[picture p20: schematic Power Supply.kicad_sch]

Parts:
C37: 4.7nF; C_0402_1005Metric
C38, C39: 47pF; C_0402_1005Metric
C40, C41, C44, C45, C46, C47: 10µF; C_0402_1005Metric
C42, C43, C48, C49, C51: CL05A106MQ5NUNC; C_0402_1005Metric
C50: 4.7µF; C_0402_1005Metric
D13: PRTR5V0U2X; SOT-143
FB1: MI0805K601R-10; L_0805_2012Metric
J7: GCT_USB4085; USB_C_Receptacle_GCT_USB4085
J8: Power Switch; PinHeader_1x02_P2.54mm_Vertical
L1, L2: 2.2µH; L_Bourns_SRN8040TA; Part No. SRN8040-2R2Y
R42: 1MΩ; R_0402_1005Metric
R43, R44: 27Ω; R_0402_1005Metric
R45, R46: 5.1KΩ; R_0402_1005Metric
R47: 0Ω; R_0402_1005Metric
R48, R49: 100Ω; R_0402_1005Metric
U10: TPS63001; Texas_DRC0010J_ThermalVias
U11: TPS63002; Texas_DRC0010J_ThermalVias
U12: FT230XS; SSOP-16_3.9x4.9mm_P0.635mm

Connections:
+3.3V: C44.2, C46.2, C51.1, U10.1 (VOUT), U10.10 (FB), U12.3 (VCCIO), U12.11 (~RESET)
+5V: C45.2, C47.2, U11.1 (VOUT), U11.10 (FB)
GND: C37.2, C38.2, C39.2, C40.1, C41.1, C42.2, C43.2, C44.1, C45.1, C46.1, C47.1, C48.2, C49.2, C50.2, C51.2, J7.A1 (GND), J7.A12 (GND), J7.B1 (GND), J7.B12 (GND), R42.2, R45.1, R46.1, U10.3 (PGND), U10.9 (GND), U10.11 (PGND), U11.3 (PGND), U11.9 (GND), U11.11 (PGND), U12.5 (GND), U12.13 (GND)
unnamed: C37.1, D13.1 (GND), J7.S1 (SHIELD), R42.1
unnamed: C38.1, D13.3 (I/O2), J7.A6 (D+), J7.B6 (D+), R44.1
unnamed: C39.1, D13.2 (I/O1), J7.A7 (D-), J7.B7 (D-), R43.1
unnamed: C41.2, R47.1, R49.2, U11.5 (VIN)
unnamed: C42.1, R48.1, U10.6 (EN), U10.7 (PS/SYNC), U10.8 (VINA)
unnamed: C43.1, R49.1, U11.6 (EN), U11.7 (PS/SYNC), U11.8 (VINA)
unnamed: FB1.1, J8.2
unnamed: J7.A4 (VBUS), J7.A9 (VBUS), J7.B4 (VBUS), J7.B9 (VBUS), J8.1
unnamed: J7.A5 (CC1), R46.2
unnamed: J7.B5 (CC2), R45.2
unnamed: L1.1, U10.4 (L1)
unnamed: L1.2, U10.2 (L2)
unnamed: L2.1, U11.4 (L1)
unnamed: L2.2, U11.2 (L2)
unnamed: R43.2, U12.9 (USBDM)
unnamed: R44.2, U12.8 (USBDP)
RXD: U12.1 (TXD)
TXD: U12.4 (RXD)
VBUS: C40.2, C48.1, C49.1, C50.1, D13.4 (VCC), FB1.2, R47.2, R48.2, U10.5 (VIN), U12.12 (VCC)
~CTS: U12.2 (~RTS)
~RTS: U12.6 (~CTS)

Notes on the sheet:
See relevant documentation for USB-C port PCB layout concerns.
