studio8502/Sentinel-65X/kicad/Sentinel 65X - Prototype 4 V2/System Memory.kicad_sch

## KiCad design kicad/Sentinel 65X - Prototype 4 V2/System Memory.kicad_sch (2024-03-15)

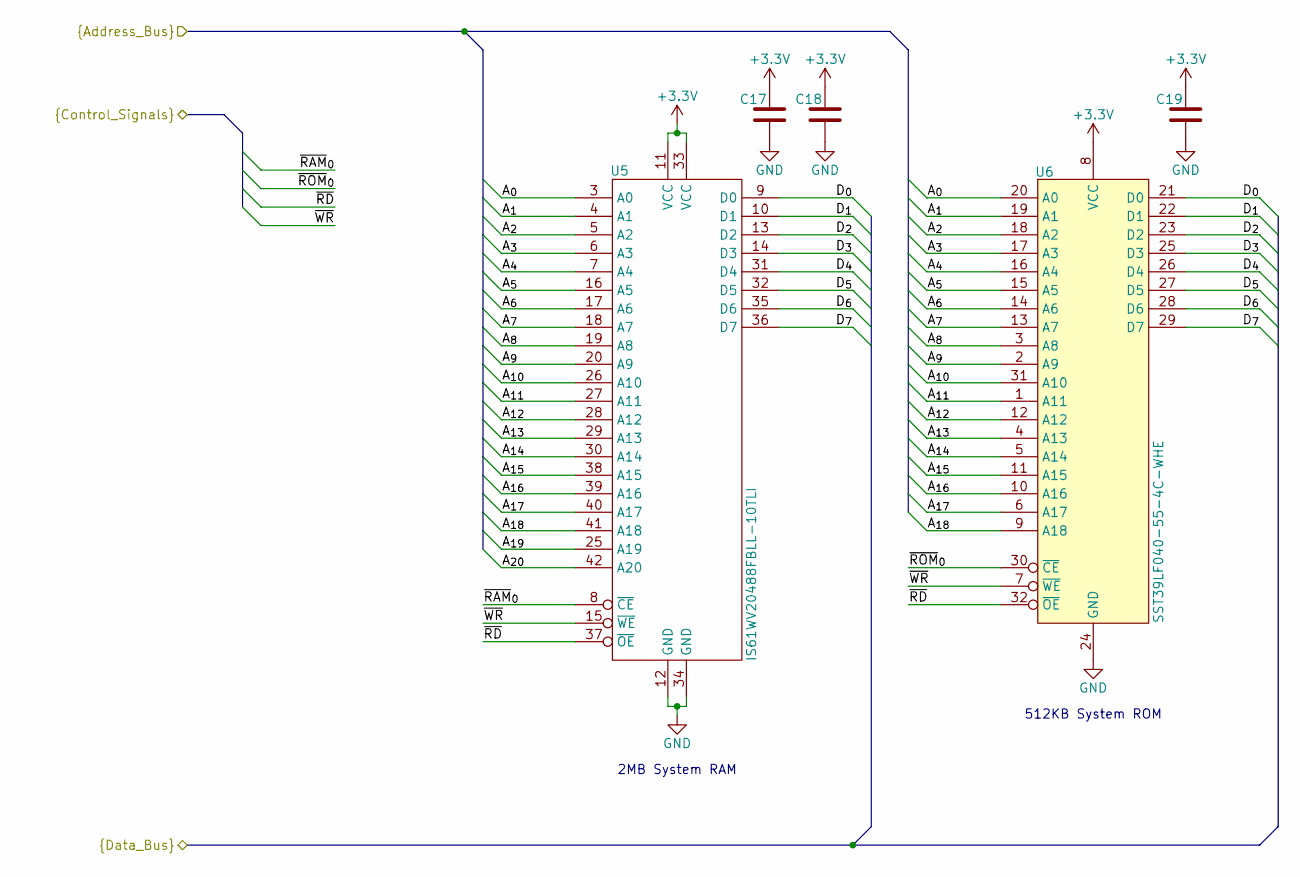
[picture p21: schematic System Memory.kicad_sch]

Parts:
C17, C18, C19: CL05A106MQ5NUNC; C_0402_1005Metric
U5: IS61WV20488FBLL-10TLI; TSOP-II-44_10.16x18.41mm_P0.8mm
U6: SST39LF040-55-4C-WHE; TSOP-I-32_14.4x8mm_P0.5mm

Connections:
+3.3V: C17.1, C18.1, C19.1, U5.11 (VCC), U5.33 (VCC), U6.8 (VCC)
A_{0}: U5.3 (A0), U6.20 (A0)
A_{1}: U5.4 (A1), U6.19 (A1)
A_{2}: U5.5 (A2), U6.18 (A2)
A_{3}: U5.6 (A3), U6.17 (A3)
A_{4}: U5.7 (A4), U6.16 (A4)
A_{5}: U5.16 (A5), U6.15 (A5)
A_{6}: U5.17 (A6), U6.14 (A6)
A_{7}: U5.18 (A7), U6.13 (A7)
A_{8}: U5.19 (A8), U6.3 (A8)
A_{9}: U5.20 (A9), U6.2 (A9)
A_{10}: U5.26 (A10), U6.31 (A10)
A_{11}: U5.27 (A11), U6.1 (A11)
A_{12}: U5.28 (A12), U6.12 (A12)
A_{13}: U5.29 (A13), U6.4 (A13)
A_{14}: U5.30 (A14), U6.5 (A14)
A_{15}: U5.38 (A15), U6.11 (A15)
A_{16}: U5.39 (A16), U6.10 (A16)
A_{17}: U5.40 (A17), U6.6 (A17)
A_{18}: U5.41 (A18), U6.9 (A18)
A_{19}: U5.25 (A19)
A_{20}: U5.42 (A20)
D_{0}: U5.9 (D0), U6.21 (D0)
D_{1}: U5.10 (D1), U6.22 (D1)
D_{2}: U5.13 (D2), U6.23 (D2)
D_{3}: U5.14 (D3), U6.25 (D3)
D_{4}: U5.31 (D4), U6.26 (D4)
D_{5}: U5.32 (D5), U6.27 (D5)
D_{6}: U5.35 (D6), U6.28 (D6)
D_{7}: U5.36 (D7), U6.29 (D7)
GND: C17.2, C18.2, C19.2, U5.12 (GND), U5.34 (GND), U6.24 (GND)
~RAM_{0}: U5.8 (~CE)
~RD: U5.37 (~OE), U6.32 (~OE)
~ROM_{0}: U6.30 (~CE)
~WR: U5.15 (~WE), U6.7 (~WE)

Notes on the sheet:
512KB System ROM
2MB System RAM
