studio8502/Sentinel-65X/kicad/Sentinel 65X - Prototype 4 V2/USB-Serial Bridge.kicad_sch

## KiCad design kicad/Sentinel 65X - Prototype 4 V2/USB-Serial Bridge.kicad_sch (2024-03-07)

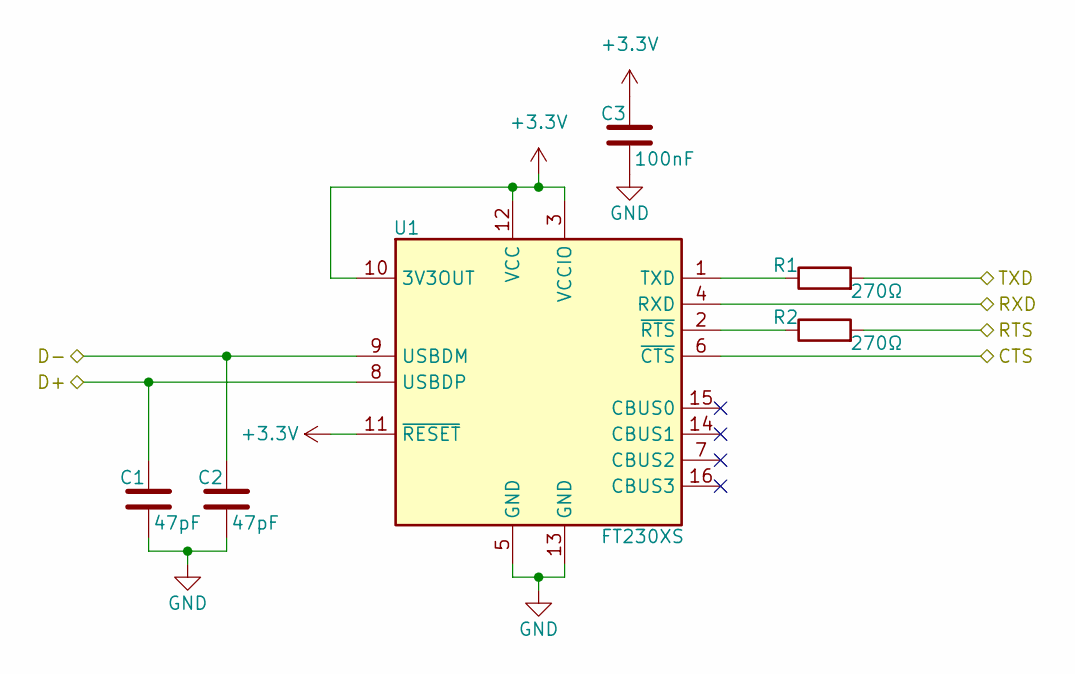
[picture p22: schematic USB-Serial Bridge.kicad_sch]

Parts:
C1, C2: 47pF; C_0402_1005Metric
C3: 100nF; C_0402_1005Metric
R1, R2: 270Ω; R_0402_1005Metric
U1: FT230XS; SSOP-16_3.9x4.9mm_P0.635mm

Connections:
+3.3V: C3.1, U1.3 (VCCIO), U1.10 (3V3OUT), U1.11 (~RESET), U1.12 (VCC)
CTS: U1.6 (~CTS)
D+: C1.1, U1.8 (USBDP)
D-: C2.1, U1.9 (USBDM)
GND: C1.2, C2.2, C3.2, U1.5 (GND), U1.13 (GND)
unnamed: R1.1, U1.1 (TXD)
unnamed: R2.1, U1.2 (~RTS)
RTS: R2.2
RXD: U1.4 (RXD)
TXD: R1.2
