studio8502/Sentinel-65X/kicad/Sentinel 65X - Prototype 4 V2/VERA.kicad_sch

## KiCad design kicad/Sentinel 65X - Prototype 4 V2/VERA.kicad_sch (2024-03-15)

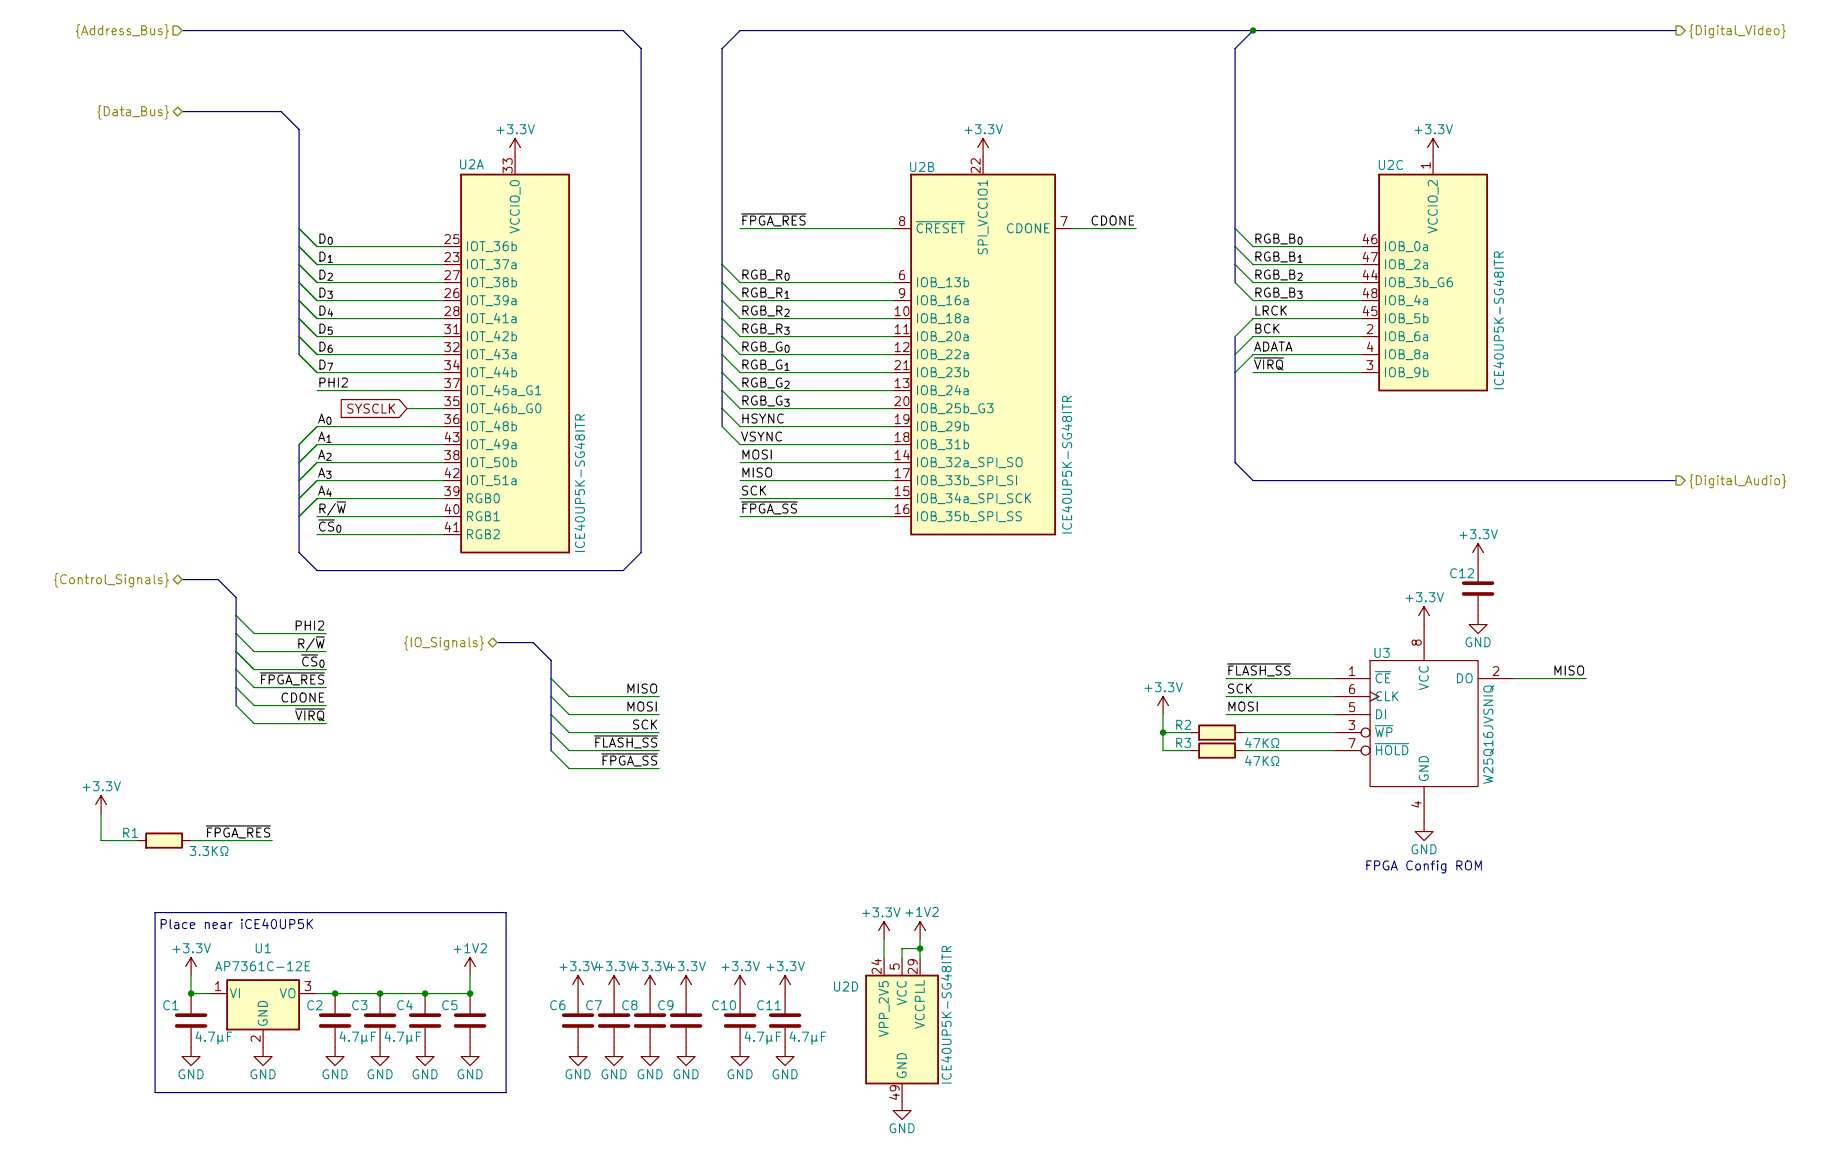
[picture p23: schematic VERA.kicad_sch]

Parts:
C1, C2, C3, C10, C11: 4.7µF; C_0402_1005Metric
C4, C5, C6, C7, C8, C9, C12: CL05A106MQ5NUNC; C_0402_1005Metric
R1: 3.3KΩ; R_0402_1005Metric
R2, R3: 47KΩ; R_0402_1005Metric
U1: AP7361C-12E; SOT-223-3_TabPin2
U2: ICE40UP5K-SG48ITR; QFN-48-1EP_7x7mm_P0.5mm_EP5.6x5.6mm
U3: W25Q16JVSNIQ; SOIC-8-1EP_3.9x4.9mm_P1.27mm_EP2.29x3mm

Connections:
+1V2: C2.1, C3.1, C4.1, C5.1, U1.3 (VO), U2.5 (VCC), U2.29 (VCCPLL), U2.30 (VCC)
+3.3V: C1.1, C6.1, C7.1, C8.1, C9.1, C10.1, C11.1, C12.1, R1.1, R2.1, R3.1, U1.1 (VI), U2.1 (VCCIO_2), U2.22 (SPI_VCCIO1), U2.24 (VPP_2V5), U2.33 (VCCIO_0), U3.8 (VCC)
ADATA: U2.4 (IOB_8a)
A_{0}: U2.36 (IOT_48b)
A_{1}: U2.43 (IOT_49a)
A_{2}: U2.38 (IOT_50b)
A_{3}: U2.42 (IOT_51a)
A_{4}: U2.39 (RGB0)
BCK: U2.2 (IOB_6a)
CDONE: U2.7 (CDONE)
D_{0}: U2.25 (IOT_36b)
D_{1}: U2.23 (IOT_37a)
D_{2}: U2.27 (IOT_38b)
D_{3}: U2.26 (IOT_39a)
D_{4}: U2.28 (IOT_41a)
D_{5}: U2.31 (IOT_42b)
D_{6}: U2.32 (IOT_43a)
D_{7}: U2.34 (IOT_44b)
GND: C1.2, C2.2, C3.2, C4.2, C5.2, C6.2, C7.2, C8.2, C9.2, C10.2, C11.2, C12.2, U1.2 (GND), U2.49 (GND), U3.4 (GND)
HSYNC: U2.19 (IOB_29b)
LRCK: U2.45 (IOB_5b)
MISO: U2.17 (IOB_33b_SPI_SI), U3.2 (DO)
MOSI: U2.14 (IOB_32a_SPI_SO), U3.5 (DI)
unnamed: R2.2, U3.3 (~WP)
unnamed: R3.2, U3.7 (~HOLD)
PHI2: U2.37 (IOT_45a_G1)
RGB_B_{0}: U2.46 (IOB_0a)
RGB_B_{1}: U2.47 (IOB_2a)
RGB_B_{2}: U2.44 (IOB_3b_G6)
RGB_B_{3}: U2.48 (IOB_4a)
RGB_G_{0}: U2.12 (IOB_22a)
RGB_G_{1}: U2.21 (IOB_23b)
RGB_G_{2}: U2.13 (IOB_24a)
RGB_G_{3}: U2.20 (IOB_25b_G3)
RGB_R_{0}: U2.6 (IOB_13b)
RGB_R_{1}: U2.9 (IOB_16a)
RGB_R_{2}: U2.10 (IOB_18a)
RGB_R_{3}: U2.11 (IOB_20a)
R/~W: U2.40 (RGB1)
SCK: U2.15 (IOB_34a_SPI_SCK), U3.6 (CLK)
SYSCLK: U2.35 (IOT_46b_G0)
VSYNC: U2.18 (IOB_31b)
~CS_{0}: U2.41 (RGB2)
~FLASH_SS: U3.1 (~CE)
~FPGA_RES: R1.2, U2.8 (~CRESET)
~FPGA_SS: U2.16 (IOB_35b_SPI_SS)
~VIRQ: U2.3 (IOB_9b)

Notes on the sheet:
FPGA Config ROM
Place near iCE40UP5K
