studio8502/Sentinel-65X/kicad/Sentinel 65X - Prototype 4 V2/W65C265S CPU.kicad_sch

## KiCad design kicad/Sentinel 65X - Prototype 4 V2/W65C265S CPU.kicad_sch (2024-03-15)

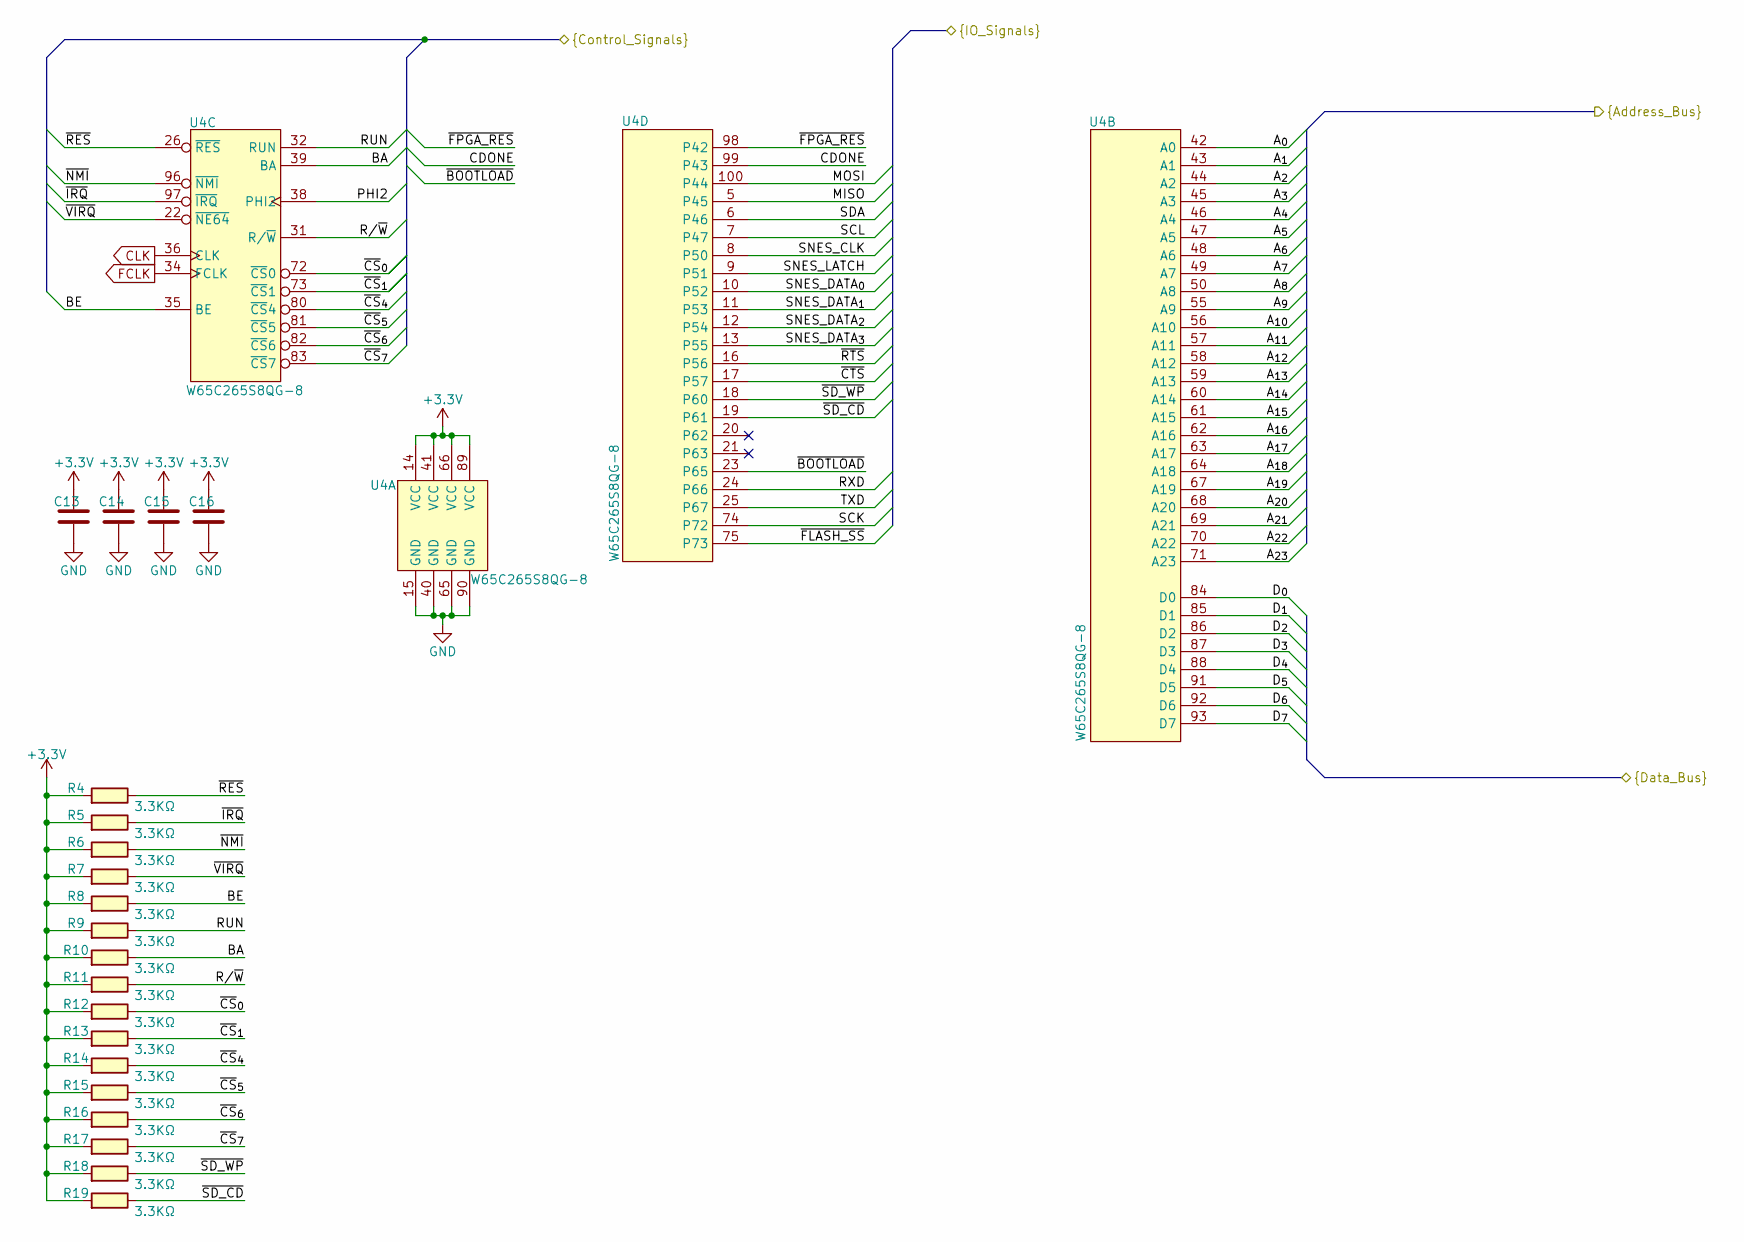
[picture p24: schematic W65C265S CPU.kicad_sch]

Parts:
C13, C14, C15, C16: CL05A106MQ5NUNC; C_0402_1005Metric
R4, R5, R6, R7, R8, R9, R10, R11, R12, R13, R14, R15, R16, R17, R18, R19: 3.3KΩ; R_0402_1005Metric
U4: W65C265S8QG-8; PQFP-100_14x20mm_P0.65mm

Connections:
+3.3V: C13.1, C14.1, C15.1, C16.1, R4.1, R5.1, R6.1, R7.1, R8.1, R9.1, R10.1, R11.1, R12.1, R13.1, R14.1, R15.1, R16.1, R17.1, R18.1, R19.1, U4.14 (VCC), U4.41 (VCC), U4.66 (VCC), U4.89 (VCC)
A_{0}: U4.42 (A0)
A_{1}: U4.43 (A1)
A_{2}: U4.44 (A2)
A_{3}: U4.45 (A3)
A_{4}: U4.46 (A4)
A_{5}: U4.47 (A5)
A_{6}: U4.48 (A6)
A_{7}: U4.49 (A7)
A_{8}: U4.50 (A8)
A_{9}: U4.55 (A9)
A_{10}: U4.56 (A10)
A_{11}: U4.57 (A11)
A_{12}: U4.58 (A12)
A_{13}: U4.59 (A13)
A_{14}: U4.60 (A14)
A_{15}: U4.61 (A15)
A_{16}: U4.62 (A16)
A_{17}: U4.63 (A17)
A_{18}: U4.64 (A18)
A_{19}: U4.67 (A19)
A_{20}: U4.68 (A20)
A_{21}: U4.69 (A21)
A_{22}: U4.70 (A22)
A_{23}: U4.71 (A23)
BA: R10.2, U4.39 (BA)
BE: R8.2, U4.35 (BE)
CDONE: U4.99 (P43)
CLK: U4.36 (CLK)
D_{0}: U4.84 (D0)
D_{1}: U4.85 (D1)
D_{2}: U4.86 (D2)
D_{3}: U4.87 (D3)
D_{4}: U4.88 (D4)
D_{5}: U4.91 (D5)
D_{6}: U4.92 (D6)
D_{7}: U4.93 (D7)
FCLK: U4.34 (FCLK)
GND: C13.2, C14.2, C15.2, C16.2, U4.15 (GND), U4.40 (GND), U4.65 (GND), U4.90 (GND)
MISO: U4.5 (P45)
MOSI: U4.100 (P44)
PHI2: U4.38 (PHI2)
RUN: R9.2, U4.32 (RUN)
RXD: U4.24 (P66)
R/~W: R11.2, U4.31 (R/~W)
SCK: U4.74 (P72)
SCL: U4.7 (P47)
SDA: U4.6 (P46)
SNES_CLK: U4.8 (P50)
SNES_DATA_{0}: U4.10 (P52)
SNES_DATA_{1}: U4.11 (P53)
SNES_DATA_{2}: U4.12 (P54)
SNES_DATA_{3}: U4.13 (P55)
SNES_LATCH: U4.9 (P51)
TXD: U4.25 (P67)
~BOOTLOAD: U4.23 (P65)
~CS_{0}: R12.2, U4.72 (~CS0)
~CS_{1}: R13.2, U4.73 (~CS1)
~CS_{4}: R14.2, U4.80 (~CS4)
~CS_{5}: R15.2, U4.81 (~CS5)
~CS_{6}: R16.2, U4.82 (~CS6)
~CS_{7}: R17.2, U4.83 (~CS7)
~CTS: U4.17 (P57)
~FLASH_SS: U4.75 (P73)
~FPGA_RES: U4.98 (P42)
~IRQ: R5.2, U4.97 (~IRQ)
~NMI: R6.2, U4.96 (~NMI)
~RES: R4.2, U4.26 (~RES)
~RTS: U4.16 (P56)
~SD_CD: R19.2, U4.19 (P61)
~SD_WP: R18.2, U4.18 (P60)
~VIRQ: R7.2, U4.22 (~NE64)
