studio8502/Sentinel-65X/kicad/Sentinel 65X - Prototype 4/Sentinel 65X - Prototype 4.kicad_sch

## KiCad design kicad/Sentinel 65X - Prototype 4/Sentinel 65X - Prototype 4.kicad_sch (2024-03-07)

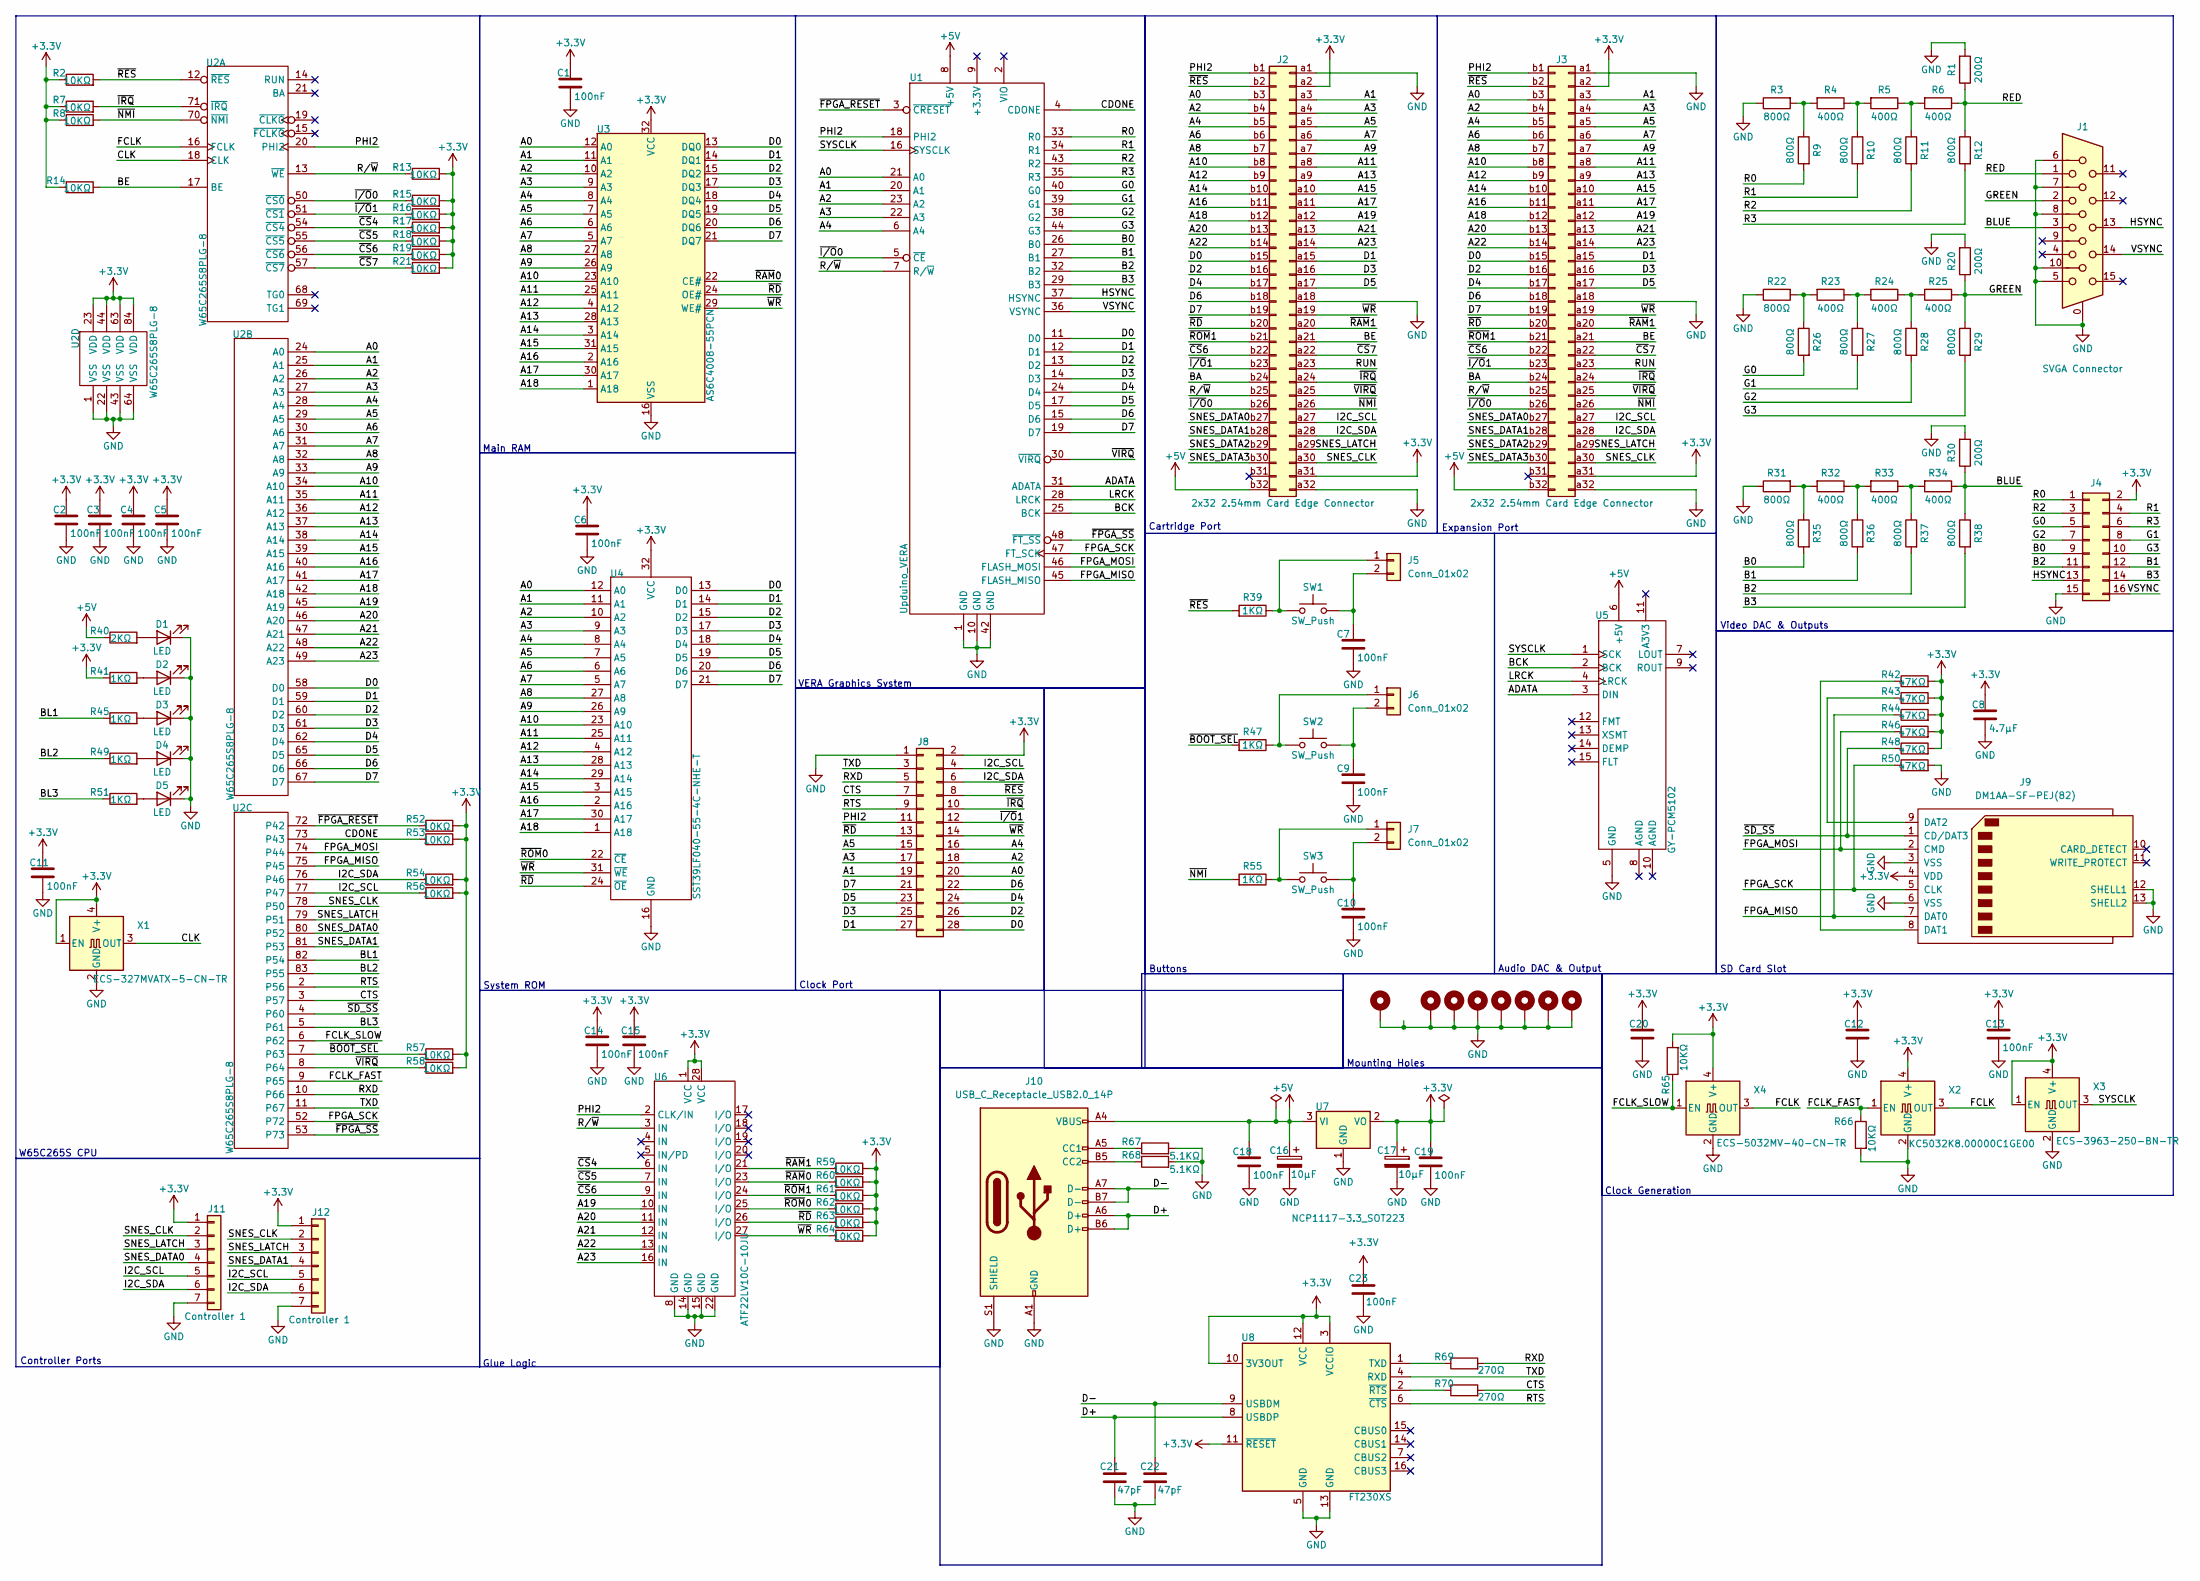
[picture p25: schematic Sentinel 65X - Prototype 4.kicad_sch]

Parts:
C1, C2, C3, C4, C5, C6, C7, C9, C10, C11, C12, C13, C14, C15, C18, C19, C20, C23: 100nF; C_0805_2012Metric
C8: 4.7µF; C_0805_2012Metric
C16, C17: 10µF; CP_Elec_4x5.4
C21, C22: 47pF; C_0805_2012Metric
D1, D2, D3, D4, D5: LED; LED_D3.0mm
H1, H3, H4, H5, H6, H7, H8, H9: MountingHole_Pad; MountingHole_3.2mm_M3_DIN965_Pad
J1: SVGA Connector; DSUB-15-HD_Female_Horizontal_P2.29x1.98mm_EdgePinOffset3.03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
J2: 2x32 2.54mm Card Edge Connector; Conn_Edge_2x32p_THT_2.54mm_5.08mm
J3: 2x32 2.54mm Card Edge Connector; Conn_Edge_2x32_THT_2.54mm_Male
J4: Conn_02x08_Odd_Even; PinSocket_2x08_P2.54mm_Vertical
J5, J6, J7: Conn_01x02; PinHeader_1x02_P2.54mm_Vertical
J8: Conn_02x14_Odd_Even; PinSocket_2x14_P2.54mm_Vertical
J9: DM1AA-SF-PEJ(82); SD_Hirose_DM1AA_SF_PEJ82
J10: USB_C_Receptacle_USB2.0_14P; USB_C_Receptacle_GCT_USB4085
J11, J12: Controller 1; SNES Controller Port (Female, 90º, THT)
R1, R20, R30: 200Ω; R_0805_2012Metric
R2, R7, R8, R13, R14, R15, R16, R17, R18, R19, R21, R52, R53, R54, R56, R57, R58, R59, R60, R61, R62, R63, R64, R65, R66: 10KΩ; R_0805_2012Metric
R3, R9, R10, R11, R12, R22, R26, R27, R28, R29, R31, R35, R36, R37, R38: 800Ω; R_0805_2012Metric
R4, R5, R6, R23, R24, R25, R32, R33, R34: 400Ω; R_0805_2012Metric
R39, R41, R45, R47, R49, R51, R55: 1KΩ; R_0805_2012Metric
R40: 2KΩ; R_0805_2012Metric
R42, R43, R44, R46, R48, R50: 47KΩ; R_0805_2012Metric
R67, R68: 5.1KΩ; R_0805_2012Metric
R69, R70: 270Ω; R_0805_2012Metric
SW1, SW2, SW3: SW_Push; SW_Tactile_Straight_KSA0Axx1LFTR
U1: Upduino_VERA; DIP-48_W17.76mm_Socket_LongPads
U2: W65C265S8PLG-8; PLCC-84_THT-Socket
U3: AS6C4008-55PCN; DIP-32_W15.24mm
U4: SST39LF040-55-4C-NHE-T; PLCC-32_THT-Socket
U5: GY-PCM5102
U6: ATF22LV10C-10JU; PLCC-28_THT-Socket
U7: NCP1117-3.3_SOT223; SOT-223-3_TabPin2
U8: FT230XS; SSOP-16_3.9x4.9mm_P0.635mm
X1: ECS-327MVATX-5-CN-TR; Oscillator_SMD_EuroQuartz_XO53-4Pin_5.0x3.2mm_HandSoldering
X2: KC5032K8.00000C1GE00; Oscillator_SMD_EuroQuartz_XO53-4Pin_5.0x3.2mm_HandSoldering
X3: ECS-3963-250-BN-TR; Oscillator_SMD_EuroQuartz_XO53-4Pin_5.0x3.2mm_HandSoldering
X4: ECS-5032MV-40-CN-TR; Oscillator_SMD_EuroQuartz_XO53-4Pin_5.0x3.2mm_HandSoldering

Connections:
+3.3V: C1.1, C2.1, C3.1, C4.1, C5.1, C6.1, C8.1, C11.1, C12.1, C13.1, C14.1, C15.1, C17.1, C19.1, C20.1, C23.1, J2.a2, J2.a31, J3.a2, J3.a31, J4.2, J8.2, J9.4 (VDD), J11.1, J12.1, R2.1, R7.1, R8.1, R13.2, R14.1, R15.2, R16.2, R17.2, R18.2, R19.2, R21.2, R41.1, R42.2, R43.2, R44.2, R46.2, R48.2, R52.2, R53.2, R54.2, R56.2, R57.2, R58.2, R59.2, R60.2, R61.2, R62.2, R63.2, R64.2, R65.2, U2.23 (VDD), U2.44 (VDD), U2.63 (VDD), U2.84 (VDD), U3.32 (VCC), U4.32 (VCC), U6.1 (VCC), U6.28 (VCC), U7.2 (VO), U8.3 (VCCIO), U8.10 (3V3OUT), U8.11 (~RESET), U8.12 (VCC), X1.1 (EN), X1.4 (V+), X2.4 (V+), X3.1 (EN), X3.4 (V+), X4.4 (V+)
+5V: C16.1, C18.1, J2.b32, J3.b32, J10.A4 (VBUS), J10.A9 (VBUS), J10.B4 (VBUS), J10.B9 (VBUS), R40.1, U1.8 (+5V), U5.6 (+5V), U7.3 (VI)
A0: J2.b3, J3.b3, J8.20, U1.21 (A0), U2.24 (A0), U3.12 (A0), U4.12 (A0)
A1: J2.a3, J3.a3, J8.19, U1.20 (A1), U2.25 (A1), U3.11 (A1), U4.11 (A1)
A2: J2.b4, J3.b4, J8.18, U1.23 (A2), U2.26 (A2), U3.10 (A2), U4.10 (A2)
A3: J2.a4, J3.a4, J8.17, U1.22 (A3), U2.27 (A3), U3.9 (A3), U4.9 (A3)
A4: J2.b5, J3.b5, J8.16, U1.6 (A4), U2.28 (A4), U3.8 (A4), U4.8 (A4)
A5: J2.a5, J3.a5, J8.15, U2.29 (A5), U3.7 (A5), U4.7 (A5)
A6: J2.b6, J3.b6, U2.30 (A6), U3.6 (A6), U4.6 (A6)
A7: J2.a6, J3.a6, U2.31 (A7), U3.5 (A7), U4.5 (A7)
A8: J2.b7, J3.b7, U2.32 (A8), U3.27 (A8), U4.27 (A8)
A9: J2.a7, J3.a7, U2.33 (A9), U3.26 (A9), U4.26 (A9)
A10: J2.b8, J3.b8, U2.34 (A10), U3.23 (A10), U4.23 (A10)
A11: J2.a8, J3.a8, U2.35 (A11), U3.25 (A11), U4.25 (A11)
A12: J2.b9, J3.b9, U2.36 (A12), U3.4 (A12), U4.4 (A12)
A13: J2.a9, J3.a9, U2.37 (A13), U3.28 (A13), U4.28 (A13)
A14: J2.b10, J3.b10, U2.38 (A14), U3.3 (A14), U4.29 (A14)
A15: J2.a10, J3.a10, U2.39 (A15), U3.31 (A15), U4.3 (A15)
A16: J2.b11, J3.b11, U2.40 (A16), U3.2 (A16), U4.2 (A16)
A17: J2.a11, J3.a11, U2.41 (A17), U3.30 (A17), U4.30 (A17)
A18: J2.b12, J3.b12, U2.42 (A18), U3.1 (A18), U4.1 (A18)
A19: J2.a12, J3.a12, U2.45 (A19), U6.10 (IN)
A20: J2.b13, J3.b13, U2.46 (A20), U6.11 (IN)
A21: J2.a13, J3.a13, U2.47 (A21), U6.12 (IN)
A22: J2.b14, J3.b14, U2.48 (A22), U6.13 (IN)
A23: J2.a14, J3.a14, U2.49 (A23), U6.16 (IN)
ADATA: U1.31 (ADATA), U5.3 (DIN)
B0: J4.9, R35.2, U1.26 (B0)
B1: J4.12, R36.2, U1.27 (B1)
B2: J4.11, R37.2, U1.32 (B2)
B3: J4.14, R38.2, U1.29 (B3)
BA: J2.b24, J3.b24
BCK: U1.25 (BCK), U5.2 (BCK)
BE: J2.a21, J3.a21, R14.2, U2.17 (BE)
BL1: R45.1, U2.82 (P54)
BL2: R49.1, U2.83 (P55)
BL3: R51.1, U2.5 (P61)
BLUE: J1.3, R30.1, R34.1, R38.1
CDONE: R53.1, U1.4 (CDONE), U2.73 (P43)
CLK: U2.18 (CLK), X1.3 (OUT)
CTS: J8.7, R70.2, U2.3 (P57)
D0: J2.b15, J3.b15, J8.28, U1.11 (D0), U2.58 (D0), U3.13 (DQ0), U4.13 (D0)
D1: J2.a15, J3.a15, J8.27, U1.12 (D1), U2.59 (D1), U3.14 (DQ1), U4.14 (D1)
D2: J2.b16, J3.b16, J8.26, U1.13 (D2), U2.60 (D2), U3.15 (DQ2), U4.15 (D2)
D3: J2.a16, J3.a16, J8.25, U1.14 (D3), U2.61 (D3), U3.17 (DQ3), U4.17 (D3)
D4: J2.b17, J3.b17, J8.24, U1.24 (D4), U2.62 (D4), U3.18 (DQ4), U4.18 (D4)
D5: J2.a17, J3.a17, J8.23, U1.17 (D5), U2.65 (D5), U3.19 (DQ5), U4.19 (D5)
D6: J2.b18, J3.b18, J8.22, U1.15 (D6), U2.66 (D6), U3.20 (DQ6), U4.20 (D6)
D7: J2.b19, J3.b19, J8.21, U1.19 (D7), U2.67 (D7), U3.21 (DQ7), U4.21 (D7)
D+: C21.1, J10.A6 (D+), J10.B6 (D+), U8.8 (USBDP)
D-: C22.1, J10.A7 (D-), J10.B7 (D-), U8.9 (USBDM)
FCLK: U2.16 (FCLK), X2.3 (OUT), X4.3 (OUT)
FCLK_FAST: R66.1, U2.9 (P65), X2.1 (EN)
FCLK_SLOW: R65.1, U2.6 (P62), X4.1 (EN)
FPGA_MISO: J9.7 (DAT0), R44.1, U1.45 (FLASH_MISO), U2.75 (P45)
FPGA_MOSI: J9.2 (CMD), R46.1, U1.46 (FLASH_MOSI), U2.74 (P44)
FPGA_SCK: J9.5 (CLK), R50.1, U1.47 (FT_SCK), U2.52 (P72)
G0: J4.5, R26.2, U1.40 (G0)
G1: J4.8, R27.2, U1.39 (G1)
G2: J4.7, R28.2, U1.38 (G2)
G3: J4.10, R29.2, U1.44 (G3)
GND: C1.2, C2.2, C3.2, C4.2, C5.2, C6.2, C7.2, C8.2, C9.2, C10.2, C11.2, C12.2, C13.2, C14.2, C15.2, C16.2, C17.2, C18.2, C19.2, C20.2, C21.2, C22.2, C23.2, D1.1 (K), D2.1 (K), D3.1 (K), D4.1 (K), D5.1 (K), H1.1, H3.1, H4.1, H5.1, H6.1, H7.1, H8.1, H9.1, J1.0, J1.5, J1.6, J1.7, J1.8, J1.10, J2.a1, J2.a18, J2.a32, J3.a1, J3.a18, J3.a32, J4.15, J8.1, J9.3 (VSS), J9.6 (VSS), J9.12 (SHELL1), J9.13 (SHELL2), J10.A1 (GND), J10.A12 (GND), J10.B1 (GND), J10.B12 (GND), J10.S1 (SHIELD), J11.7, J12.7, R1.2, R3.1, R20.2, R22.1, R30.2, R31.1, R50.2, R66.2, R67.2, R68.2, U1.1 (GND), U1.10 (GND), U1.42 (GND), U2.1 (VSS), U2.22 (VSS), U2.43 (VSS), U2.64 (VSS), U3.16 (VSS), U4.16 (GND), U5.5 (GND), U6.8 (GND), U6.14 (GND), U6.15 (GND), U6.22 (GND), U7.1 (GND), U8.5 (GND), U8.13 (GND), X1.2 (GND), X2.2 (GND), X3.2 (GND), X4.2 (GND)
GREEN: J1.2, R20.1, R25.1, R29.1
HSYNC: J1.13, J4.13, U1.37 (HSYNC)
I2C_SCL: J2.a27, J3.a27, J8.4, J11.5, J12.5, R56.1, U2.77 (P47)
I2C_SDA: J2.a28, J3.a28, J8.6, J11.6, J12.6, R54.1, U2.76 (P46)
LRCK: U1.28 (LRCK), U5.4 (LRCK)
unnamed: C7.1, J5.2, SW1.2
unnamed: C9.1, J6.2, SW2.2
unnamed: C10.1, J7.2, SW3.2
unnamed: D1.2 (A), R40.2
unnamed: D2.2 (A), R41.2
unnamed: D3.2 (A), R45.2
unnamed: D4.2 (A), R49.2
unnamed: D5.2 (A), R51.2
unnamed: J5.1, R39.1, SW1.1
unnamed: J6.1, R47.1, SW2.1
unnamed: J7.1, R55.1, SW3.1
unnamed: J9.8 (DAT1), R42.1
unnamed: J9.9 (DAT2), R43.1
unnamed: J10.A5 (CC1), R67.1
unnamed: J10.B5 (CC2), R68.1
unnamed: R3.2, R4.2, R9.1
unnamed: R4.1, R5.2, R10.1
unnamed: R5.1, R6.2, R11.1
unnamed: R22.2, R23.2, R26.1
unnamed: R23.1, R24.2, R27.1
unnamed: R24.1, R25.2, R28.1
unnamed: R31.2, R32.2, R35.1
unnamed: R32.1, R33.2, R36.1
unnamed: R33.1, R34.2, R37.1
unnamed: R69.1, U8.1 (TXD)
unnamed: R70.1, U8.2 (~RTS)
PHI2: J2.b1, J3.b1, J8.11, U1.18 (PHI2), U2.20 (PHI2), U6.2 (CLK/IN)
R0: J4.1, R9.2, U1.33 (R0)
R1: J4.4, R10.2, U1.34 (R1)
R2: J4.3, R11.2, U1.43 (R2)
R3: J4.6, R12.2, U1.35 (R3)
RED: J1.1, R1.1, R6.1, R12.1
RTS: J8.9, U2.2 (P56), U8.6 (~CTS)
RUN: J2.a23, J3.a23
RXD: J8.5, R69.2, U2.10 (P66)
R/~W: J2.b25, J3.b25, R13.1, U1.7 (R/~W), U2.13 (~WE), U6.3 (IN)
SNES_CLK: J2.a30, J3.a30, J11.2, J12.2, U2.78 (P50)
SNES_DATA0: J2.b27, J3.b27, J11.4, U2.80 (P52)
SNES_DATA1: J2.b28, J3.b28, J12.4, U2.81 (P53)
SNES_DATA2: J2.b29, J3.b29
SNES_DATA3: J2.b30, J3.b30
SNES_LATCH: J2.a29, J3.a29, J11.3, J12.3, U2.79 (P51)
SYSCLK: U1.16 (SYSCLK), U5.1 (SCK), X3.3 (OUT)
TXD: J8.3, U2.11 (P67), U8.4 (RXD)
VSYNC: J1.14, J4.16, U1.36 (VSYNC)
~BOOT_SEL: R47.2, R57.1, U2.7 (P63)
~CS4: R17.1, U2.54 (~CS4), U6.6 (IN)
~CS5: R18.1, U2.55 (~CS5), U6.7 (IN)
~CS6: J2.b22, J3.b22, R19.1, U2.56 (~CS6), U6.9 (IN)
~CS7: J2.a22, J3.a22, R21.1, U2.57 (~CS7)
~FPGA_RESET: R52.1, U1.3 (~CRESET), U2.72 (P42)
~FPGA_SS: U1.48 (~FT_SS), U2.53 (P73)
~IRQ: J2.a24, J3.a24, J8.10, R7.2, U2.71 (~IRQ)
~I/O0: J2.b26, J3.b26, R15.1, U1.5 (~CE), U2.50 (~CS0)
~I/O1: J2.b23, J3.b23, J8.12, R16.1, U2.51 (~CS1)
~NMI: J2.a26, J3.a26, R8.2, R55.2, U2.70 (~NMI)
~RAM0: R60.1, U3.22 (CE#), U6.23 (I/O)
~RAM1: J2.a20, J3.a20, R59.1, U6.21 (I/O)
~RD: J2.b20, J3.b20, J8.13, R63.1, U3.24 (OE#), U4.24 (~OE), U6.26 (I/O)
~RES: J2.b2, J3.b2, J8.8, R2.2, R39.2, U2.12 (~RES)
~ROM0: R62.1, U4.22 (~CE), U6.25 (I/O)
~ROM1: J2.b21, J3.b21, R61.1, U6.24 (I/O)
~SD_SS: J9.1 (CD/DAT3), R48.1, U2.4 (P60)
~VIRQ: J2.a25, J3.a25, R58.1, U1.30 (~VIRQ), U2.8 (P64)
~WR: J2.a19, J3.a19, J8.14, R64.1, U3.29 (WE#), U4.31 (~WE), U6.27 (I/O)

Notes on the sheet:
SD Card Slot
Audio DAC & Output
Cartridge Port
W65C265S CPU
Controller Ports
System ROM
Clock Port
VERA Graphics System
Clock Generation
Video DAC & Outputs
Main RAM
Glue Logic
Buttons
Mounting Holes
Expansion Port
