studio8502/Sentinel-65X/kicad/Sentinel 65X Expansion Backplane/Sentinel 65X Expansion Backplane.kicad_sch

## KiCad design kicad/Sentinel 65X Expansion Backplane/Sentinel 65X Expansion Backplane.kicad_sch (2024-03-07)

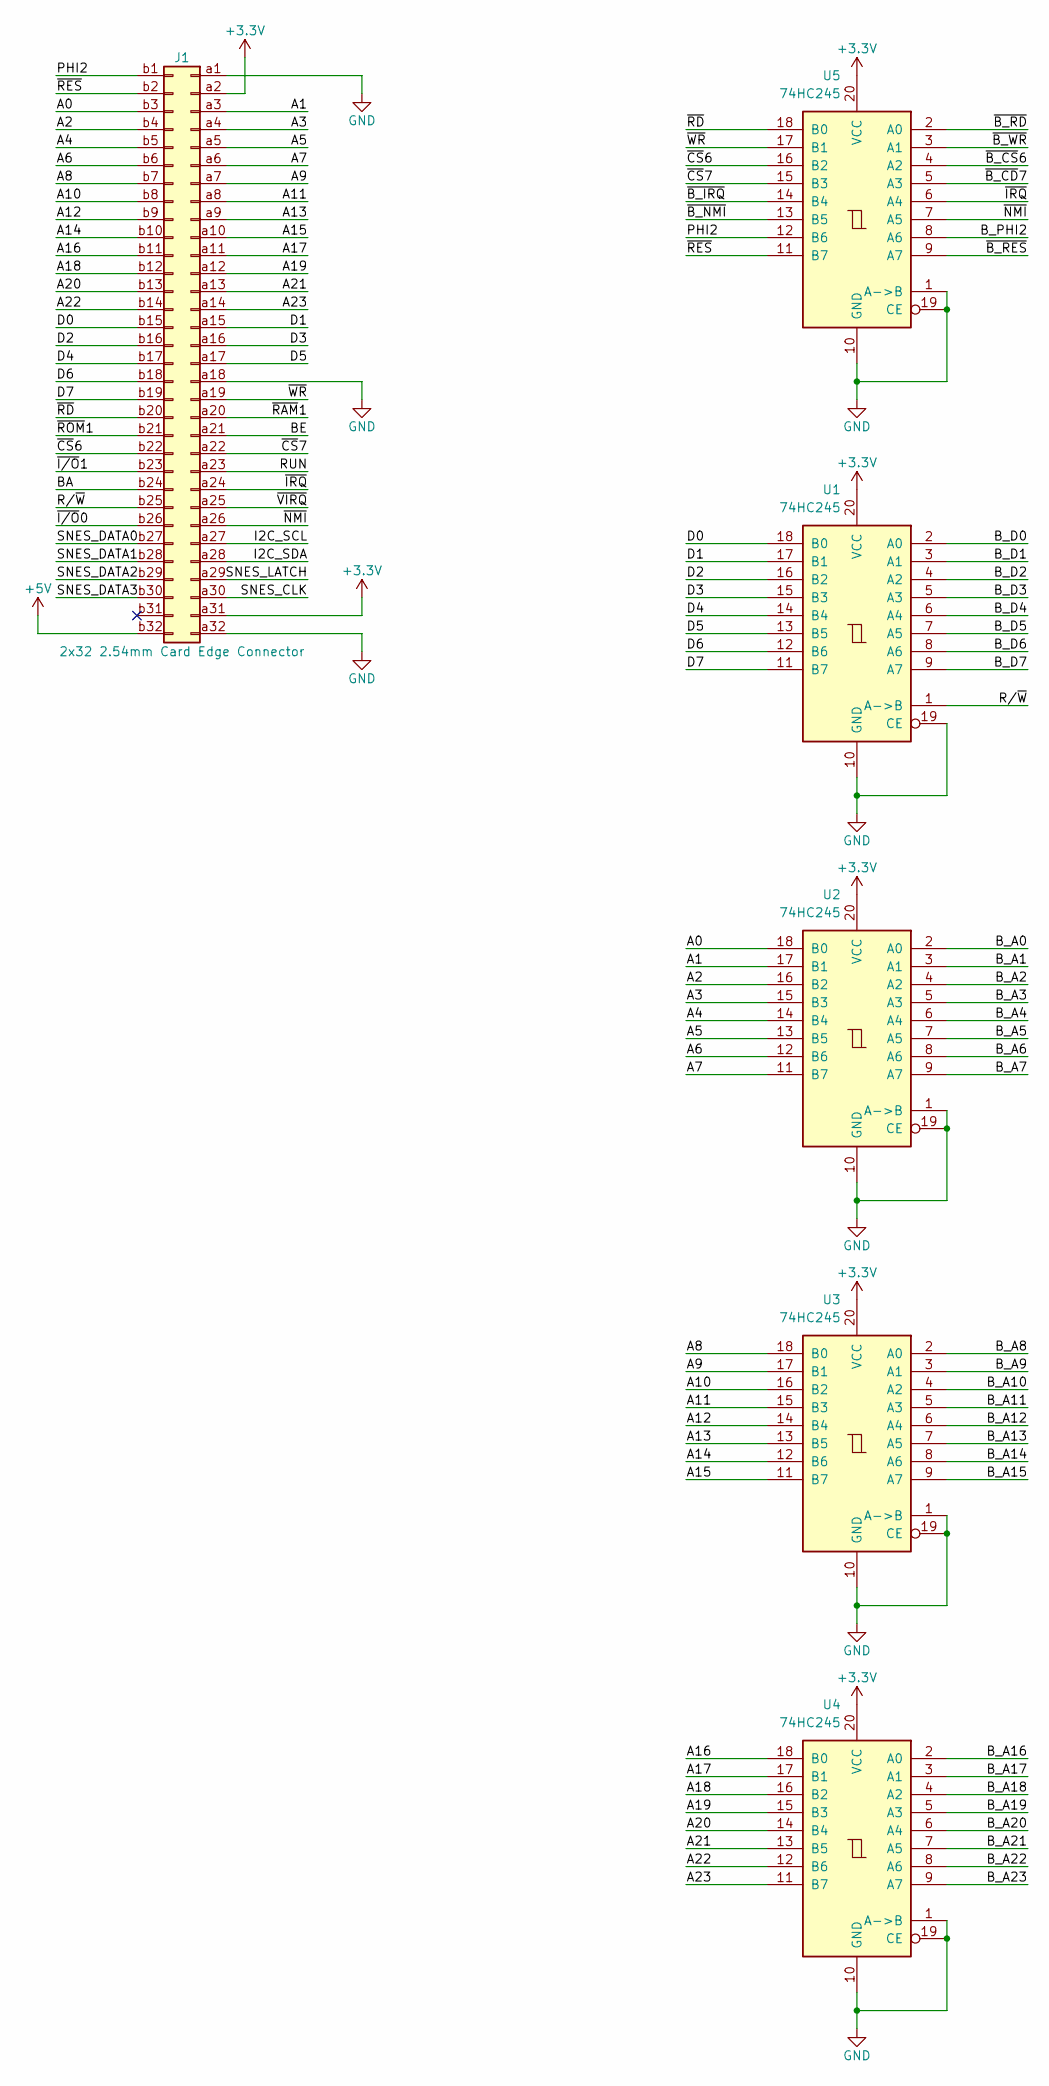
[picture p26: schematic Sentinel 65X Expansion Backplane.kicad_sch]

Parts:
J1: 2x32 2.54mm Card Edge Connector; Conn_Edge_2x32_THT_2.54mm_Male
U1, U2, U3, U4, U5: 74HC245

Connections:
+3.3V: J1.a2, J1.a31, U1.20 (VCC), U2.20 (VCC), U3.20 (VCC), U4.20 (VCC), U5.20 (VCC)
+5V: J1.b32
A0: J1.b3, U2.18 (B0)
A1: J1.a3, U2.17 (B1)
A2: J1.b4, U2.16 (B2)
A3: J1.a4, U2.15 (B3)
A4: J1.b5, U2.14 (B4)
A5: J1.a5, U2.13 (B5)
A6: J1.b6, U2.12 (B6)
A7: J1.a6, U2.11 (B7)
A8: J1.b7, U3.18 (B0)
A9: J1.a7, U3.17 (B1)
A10: J1.b8, U3.16 (B2)
A11: J1.a8, U3.15 (B3)
A12: J1.b9, U3.14 (B4)
A13: J1.a9, U3.13 (B5)
A14: J1.b10, U3.12 (B6)
A15: J1.a10, U3.11 (B7)
A16: J1.b11, U4.18 (B0)
A17: J1.a11, U4.17 (B1)
A18: J1.b12, U4.16 (B2)
A19: J1.a12, U4.15 (B3)
A20: J1.b13, U4.14 (B4)
A21: J1.a13, U4.13 (B5)
A22: J1.b14, U4.12 (B6)
A23: J1.a14, U4.11 (B7)
BA: J1.b24
BE: J1.a21
B_A0: U2.2 (A0)
B_A1: U2.3 (A1)
B_A2: U2.4 (A2)
B_A3: U2.5 (A3)
B_A4: U2.6 (A4)
B_A5: U2.7 (A5)
B_A6: U2.8 (A6)
B_A7: U2.9 (A7)
B_A8: U3.2 (A0)
B_A9: U3.3 (A1)
B_A10: U3.4 (A2)
B_A11: U3.5 (A3)
B_A12: U3.6 (A4)
B_A13: U3.7 (A5)
B_A14: U3.8 (A6)
B_A15: U3.9 (A7)
B_A16: U4.2 (A0)
B_A17: U4.3 (A1)
B_A18: U4.4 (A2)
B_A19: U4.5 (A3)
B_A20: U4.6 (A4)
B_A21: U4.7 (A5)
B_A22: U4.8 (A6)
B_A23: U4.9 (A7)
B_D0: U1.2 (A0)
B_D1: U1.3 (A1)
B_D2: U1.4 (A2)
B_D3: U1.5 (A3)
B_D4: U1.6 (A4)
B_D5: U1.7 (A5)
B_D6: U1.8 (A6)
B_D7: U1.9 (A7)
B_PHI2: U5.8 (A6)
D0: J1.b15, U1.18 (B0)
D1: J1.a15, U1.17 (B1)
D2: J1.b16, U1.16 (B2)
D3: J1.a16, U1.15 (B3)
D4: J1.b17, U1.14 (B4)
D5: J1.a17, U1.13 (B5)
D6: J1.b18, U1.12 (B6)
D7: J1.b19, U1.11 (B7)
GND: J1.a1, J1.a18, J1.a32, U1.10 (GND), U1.19 (CE), U2.1 (A->B), U2.10 (GND), U2.19 (CE), U3.1 (A->B), U3.10 (GND), U3.19 (CE), U4.1 (A->B), U4.10 (GND), U4.19 (CE), U5.1 (A->B), U5.10 (GND), U5.19 (CE)
I2C_SCL: J1.a27
I2C_SDA: J1.a28
PHI2: J1.b1, U5.12 (B6)
RUN: J1.a23
R/~W: J1.b25, U1.1 (A->B)
SNES_CLK: J1.a30
SNES_DATA0: J1.b27
SNES_DATA1: J1.b28
SNES_DATA2: J1.b29
SNES_DATA3: J1.b30
SNES_LATCH: J1.a29
~B_CD7: U5.5 (A3)
~B_CS6: U5.4 (A2)
~B_IRQ: U5.14 (B4)
~B_NMI: U5.13 (B5)
~B_RD: U5.2 (A0)
~B_RES: U5.9 (A7)
~B_WR: U5.3 (A1)
~CS6: J1.b22, U5.16 (B2)
~CS7: J1.a22, U5.15 (B3)
~IRQ: J1.a24, U5.6 (A4)
~I/O0: J1.b26
~I/O1: J1.b23
~NMI: J1.a26, U5.7 (A5)
~RAM1: J1.a20
~RD: J1.b20, U5.18 (B0)
~RES: J1.b2, U5.11 (B7)
~ROM1: J1.b21
~VIRQ: J1.a25
~WR: J1.a19, U5.17 (B1)
