studio8502/Sentinel-65X/kicad/Sentinel 65X Keyboard - V01/Sentinel 65X Keyboard - V01.kicad_sch

## KiCad design kicad/Sentinel 65X Keyboard - V01/Sentinel 65X Keyboard - V01.kicad_sch (2024-03-07)

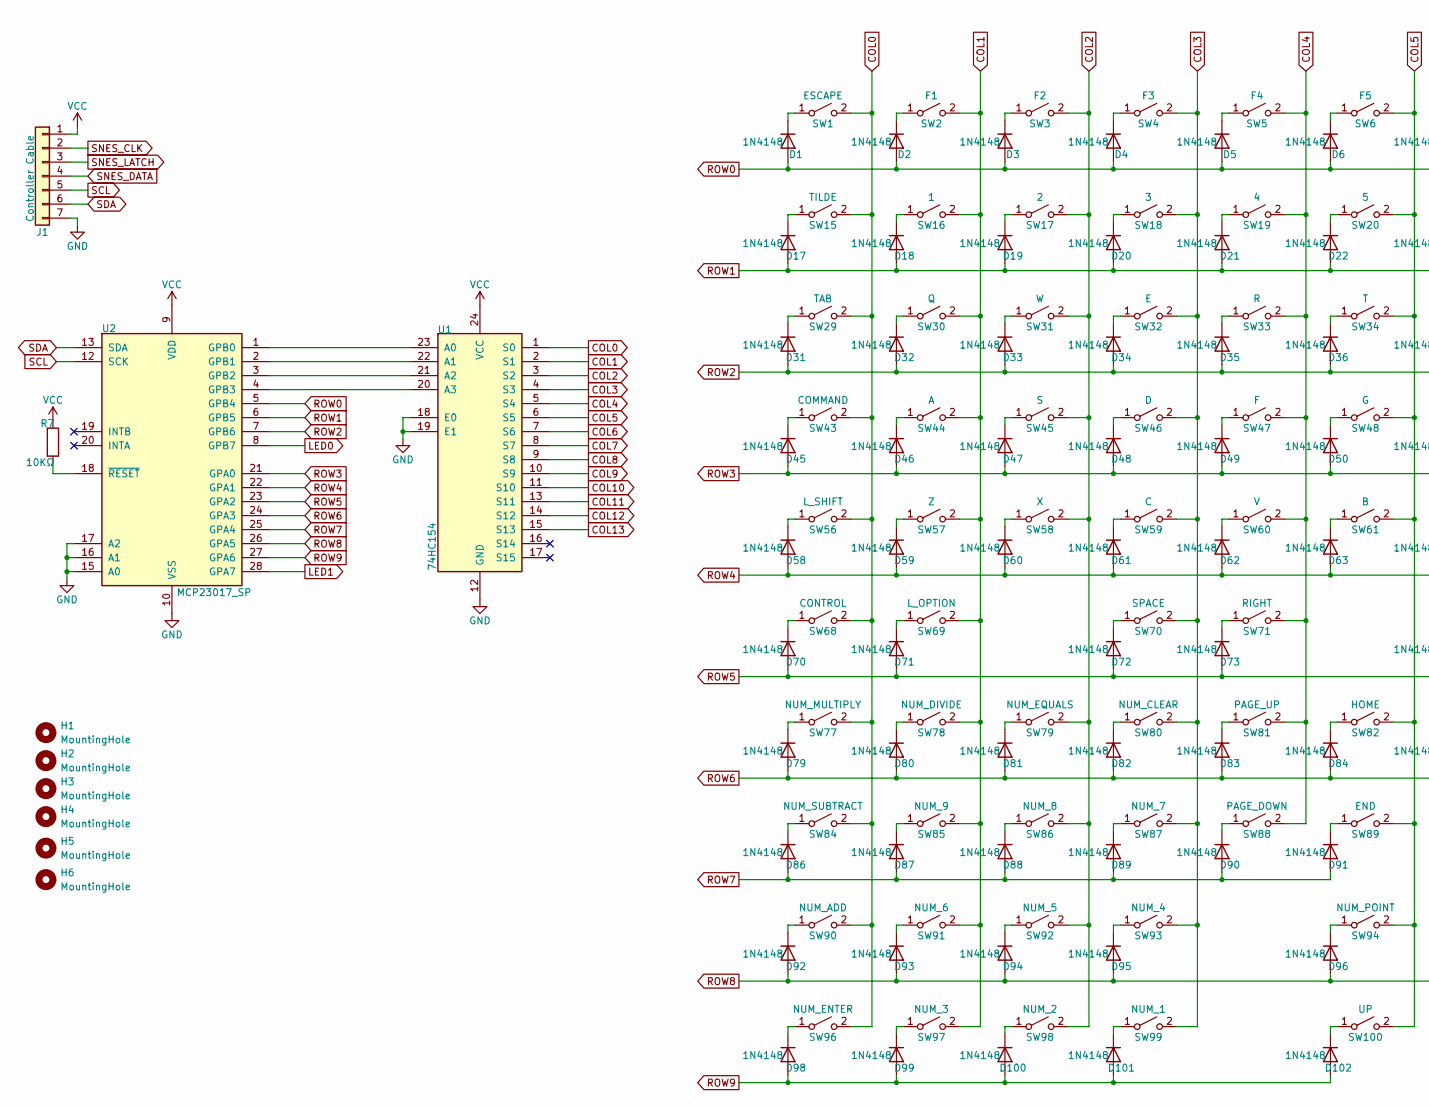
[picture p27: schematic Sentinel 65X Keyboard - V01.kicad_sch, part in row 1, column 1]

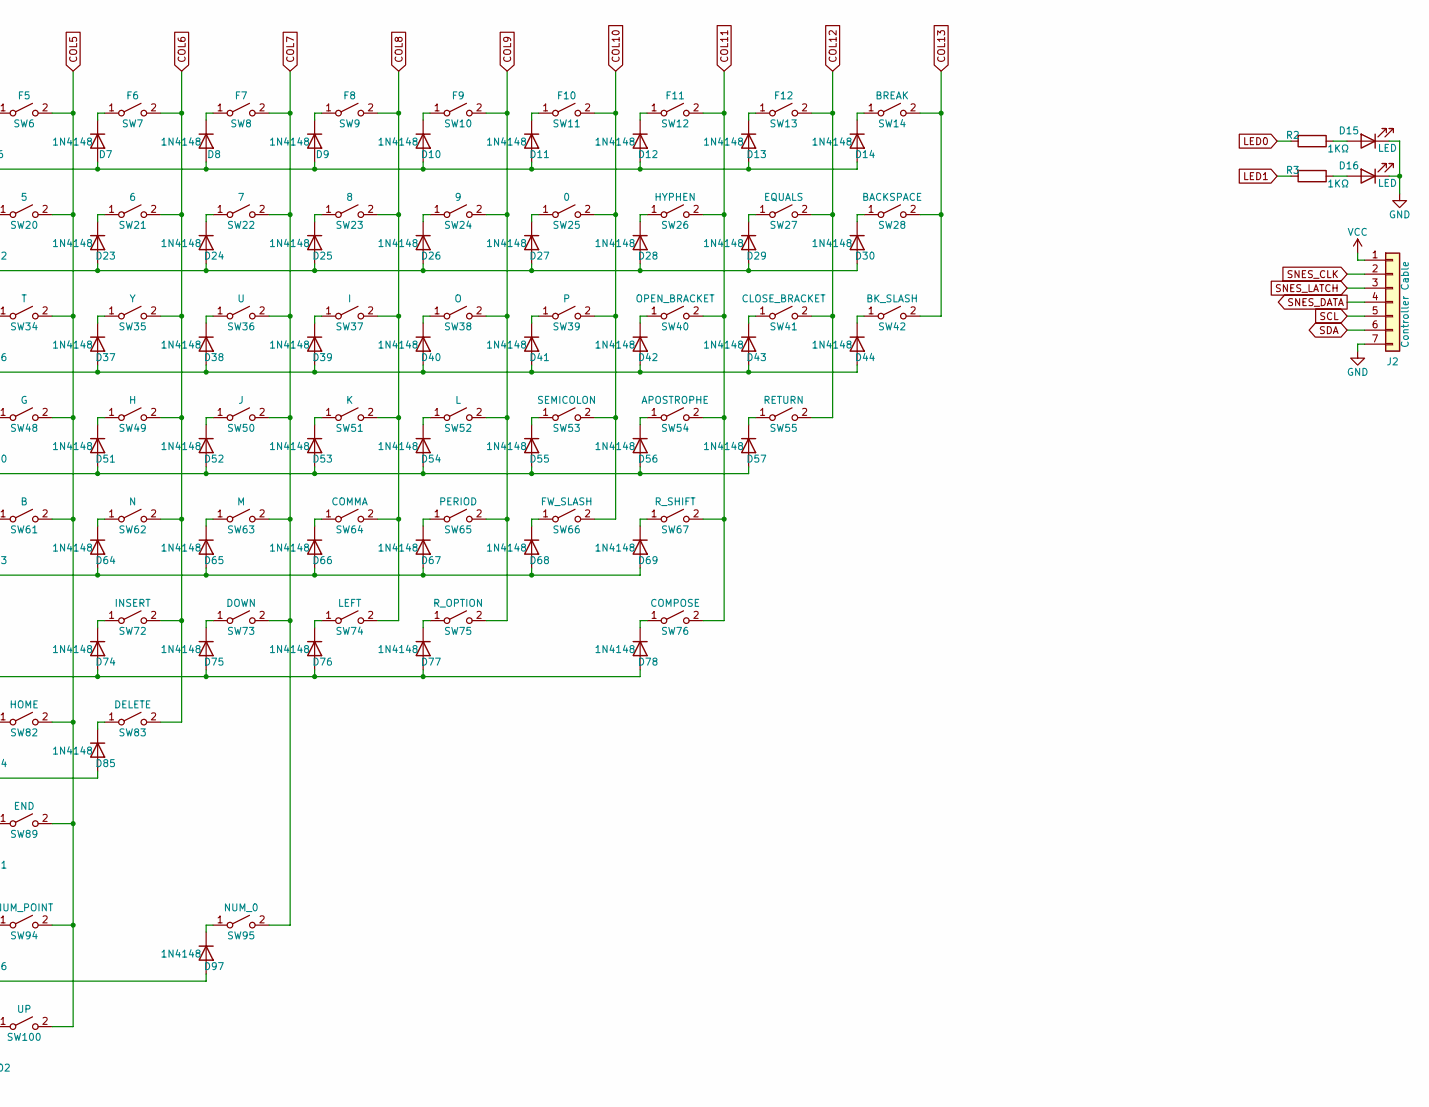
[picture p28: schematic Sentinel 65X Keyboard - V01.kicad_sch, part in row 1, column 2]

Parts:
D1, D2, D3, D4, D5, D6, D7, D8, D9, D10, D11, D12, D13, D14, D17, D18, D19, D20, D21, D22, D23, D24, D25, D26, D27, D28, D29, D30, D31, D32, D33, D34, D35, D36, D37, D38, D39, D40, D41, D42, D43, D44, D45, D46, D47, D48, D49, D50, D51, D52, D53, D54, D55, D56, D57, D58, D59, D60, D61, D62, D63, D64, D65, D66, D67, D68, D69, D70, D71, D72, D73, D74, D75, D76, D77, D78, D79, D80, D81, D82, D83, D84, D85, D86, D87, D88, D89, D90, D91, D92, D93, D94, D95, D96, D97, D98, D99, D100, D101, D102: 1N4148; D_SOD-323F
D15, D16: LED; LED_D3.0mm
H1, H2, H3, H4, H5, H6: MountingHole; MountingHole_3.2mm_M3_DIN965
J1: Controller Cable; PinHeader_1x07_P2.54mm_Vertical
J2: Controller Cable; SNES Controller Port (Female, 90º, THT)
R2, R3: 1KΩ; R_0402_1005Metric
R7: 10KΩ; R_0402_1005Metric
SW1: ESCAPE; SW_Cherry_MX_1.00u_PCB
SW2: F1; SW_Cherry_MX_1.00u_PCB
SW3: F2; SW_Cherry_MX_1.00u_PCB
SW4: F3; SW_Cherry_MX_1.00u_PCB
SW5: F4; SW_Cherry_MX_1.00u_PCB
SW6: F5; SW_Cherry_MX_1.00u_PCB
SW7: F6; SW_Cherry_MX_1.00u_PCB
SW8: F7; SW_Cherry_MX_1.00u_PCB
SW9: F8; SW_Cherry_MX_1.00u_PCB
SW10: F9; SW_Cherry_MX_1.00u_PCB
SW11: F10; SW_Cherry_MX_1.00u_PCB
SW12: F11; SW_Cherry_MX_1.00u_PCB
SW13: F12; SW_Cherry_MX_1.00u_PCB
SW14: BREAK; SW_Cherry_MX_1.25u_PCB
SW15: TILDE; SW_Cherry_MX_1.00u_PCB
SW16: 1; SW_Cherry_MX_1.00u_PCB
SW17: 2; SW_Cherry_MX_1.00u_PCB
SW18: 3; SW_Cherry_MX_1.00u_PCB
SW19: 4; SW_Cherry_MX_1.00u_PCB
SW20: 5; SW_Cherry_MX_1.00u_PCB
SW21: 6; SW_Cherry_MX_1.00u_PCB
SW22: 7; SW_Cherry_MX_1.00u_PCB
SW23: 8; SW_Cherry_MX_1.00u_PCB
SW24: 9; SW_Cherry_MX_1.00u_PCB
SW25: 0; SW_Cherry_MX_1.00u_PCB
SW26: HYPHEN; SW_Cherry_MX_1.00u_PCB
SW27: EQUALS; SW_Cherry_MX_1.00u_PCB
SW28: BACKSPACE; SW_Cherry_MX_2.00u_PCB
SW29: TAB; SW_Cherry_MX_1.50u_PCB
SW30: Q; SW_Cherry_MX_1.00u_PCB
SW31: W; SW_Cherry_MX_1.00u_PCB
SW32: E; SW_Cherry_MX_1.00u_PCB
SW33: R; SW_Cherry_MX_1.00u_PCB
SW34: T; SW_Cherry_MX_1.00u_PCB
SW35: Y; SW_Cherry_MX_1.00u_PCB
SW36: U; SW_Cherry_MX_1.00u_PCB
SW37: I; SW_Cherry_MX_1.00u_PCB
SW38: O; SW_Cherry_MX_1.00u_PCB
SW39: P; SW_Cherry_MX_1.00u_PCB
SW40: OPEN_BRACKET; SW_Cherry_MX_1.00u_PCB
SW41: CLOSE_BRACKET; SW_Cherry_MX_1.00u_PCB
SW42: BK_SLASH; SW_Cherry_MX_1.50u_PCB
SW43: COMMAND; SW_Cherry_MX_1.75u_PCB
SW44: A; SW_Cherry_MX_1.00u_PCB
SW45: S; SW_Cherry_MX_1.00u_PCB
SW46: D; SW_Cherry_MX_1.00u_PCB
SW47: F; SW_Cherry_MX_1.00u_PCB
SW48: G; SW_Cherry_MX_1.00u_PCB
SW49: H; SW_Cherry_MX_1.00u_PCB
SW50: J; SW_Cherry_MX_1.00u_PCB
SW51: K; SW_Cherry_MX_1.00u_PCB
SW52: L; SW_Cherry_MX_1.00u_PCB
SW53: SEMICOLON; SW_Cherry_MX_1.00u_PCB
SW54: APOSTROPHE; SW_Cherry_MX_1.00u_PCB
SW55: RETURN; SW_Cherry_MX_2.25u_PCB
SW56: L_SHIFT; SW_Cherry_MX_2.25u_PCB
SW57: Z; SW_Cherry_MX_1.00u_PCB
SW58: X; SW_Cherry_MX_1.00u_PCB
SW59: C; SW_Cherry_MX_1.00u_PCB
SW60: V; SW_Cherry_MX_1.00u_PCB
SW61: B; SW_Cherry_MX_1.00u_PCB
SW62: N; SW_Cherry_MX_1.00u_PCB
SW63: M; SW_Cherry_MX_1.00u_PCB
SW64: COMMA; SW_Cherry_MX_1.00u_PCB
SW65: PERIOD; SW_Cherry_MX_1.00u_PCB
SW66: FW_SLASH; SW_Cherry_MX_1.00u_PCB
SW67: R_SHIFT; SW_Cherry_MX_2.75u_PCB
SW68: CONTROL; SW_Cherry_MX_1.75u_PCB
SW69: L_OPTION; SW_Cherry_MX_1.75u_PCB
SW70: SPACE; SW_Cherry_MX_6.25u_PCB
SW71: RIGHT; SW_Cherry_MX_1.00u_PCB
SW72: INSERT; SW_Cherry_MX_1.00u_PCB
SW73: DOWN; SW_Cherry_MX_1.00u_PCB
SW74: LEFT; SW_Cherry_MX_1.00u_PCB
SW75: R_OPTION; SW_Cherry_MX_1.75u_PCB
SW76: COMPOSE; SW_Cherry_MX_1.75u_PCB
SW77: NUM_MULTIPLY; SW_Cherry_MX_1.00u_PCB
SW78: NUM_DIVIDE; SW_Cherry_MX_1.00u_PCB
SW79: NUM_EQUALS; SW_Cherry_MX_1.00u_PCB
SW80: NUM_CLEAR; SW_Cherry_MX_1.00u_PCB
SW81: PAGE_UP; SW_Cherry_MX_1.00u_PCB
SW82: HOME; SW_Cherry_MX_1.00u_PCB
SW83: DELETE; SW_Cherry_MX_1.00u_PCB
SW84: NUM_SUBTRACT; SW_Cherry_MX_1.00u_PCB
SW85: NUM_9; SW_Cherry_MX_1.00u_PCB
SW86: NUM_8; SW_Cherry_MX_1.00u_PCB
SW87: NUM_7; SW_Cherry_MX_1.00u_PCB
SW88: PAGE_DOWN; SW_Cherry_MX_1.00u_PCB
SW89: END; SW_Cherry_MX_1.00u_PCB
SW90: NUM_ADD; SW_Cherry_MX_1.00u_PCB
SW91: NUM_6; SW_Cherry_MX_1.00u_PCB
SW92: NUM_5; SW_Cherry_MX_1.00u_PCB
SW93: NUM_4; SW_Cherry_MX_1.00u_PCB
SW94: NUM_POINT; SW_Cherry_MX_1.00u_PCB
SW95: NUM_0; SW_Cherry_MX_2.00u_PCB
SW96: NUM_ENTER; SW_Cherry_MX_2.00u_Vertical_PCB
SW97: NUM_3; SW_Cherry_MX_1.00u_PCB
SW98: NUM_2; SW_Cherry_MX_1.00u_PCB
SW99: NUM_1; SW_Cherry_MX_1.00u_PCB
SW100: UP; SW_Cherry_MX_1.00u_PCB
U1: 74HC154; SOIC-24W_7.5x15.4mm_P1.27mm
U2: MCP23017_SP; SOIC-28W_7.5x18.7mm_P1.27mm

Connections:
COL0: SW1.2 (B), SW15.2 (B), SW29.2 (B), SW43.2 (B), SW56.2 (B), SW68.2 (B), SW77.2 (B), SW84.2 (B), SW90.2 (B), SW96.2 (B), U1.1 (S0)
COL1: SW2.2 (B), SW16.2 (B), SW30.2 (B), SW44.2 (B), SW57.2 (B), SW69.2 (B), SW78.2 (B), SW85.2 (B), SW91.2 (B), SW97.2 (B), U1.2 (S1)
COL2: SW3.2 (B), SW17.2 (B), SW31.2 (B), SW45.2 (B), SW58.2 (B), SW79.2 (B), SW86.2 (B), SW92.2 (B), SW98.2 (B), U1.3 (S2)
COL3: SW4.2 (B), SW18.2 (B), SW32.2 (B), SW46.2 (B), SW59.2 (B), SW70.2 (B), SW80.2 (B), SW87.2 (B), SW93.2 (B), SW99.2 (B), U1.4 (S3)
COL4: SW5.2 (B), SW19.2 (B), SW33.2 (B), SW47.2 (B), SW60.2 (B), SW71.2 (B), SW81.2 (B), SW88.2 (B), U1.5 (S4)
COL5: SW6.2 (B), SW20.2 (B), SW34.2 (B), SW48.2 (B), SW61.2 (B), SW82.2 (B), SW89.2 (B), SW94.2 (B), SW100.2 (B), U1.6 (S5)
COL6: SW7.2 (B), SW21.2 (B), SW35.2 (B), SW49.2 (B), SW62.2 (B), SW72.2 (B), SW83.2 (B), U1.7 (S6)
COL7: SW8.2 (B), SW22.2 (B), SW36.2 (B), SW50.2 (B), SW63.2 (B), SW73.2 (B), SW95.2 (B), U1.8 (S7)
COL8: SW9.2 (B), SW23.2 (B), SW37.2 (B), SW51.2 (B), SW64.2 (B), SW74.2 (B), U1.9 (S8)
COL9: SW10.2 (B), SW24.2 (B), SW38.2 (B), SW52.2 (B), SW65.2 (B), SW75.2 (B), U1.10 (S9)
COL10: SW11.2 (B), SW25.2 (B), SW39.2 (B), SW53.2 (B), SW66.2 (B), U1.11 (S10)
COL11: SW12.2 (B), SW26.2 (B), SW40.2 (B), SW54.2 (B), SW67.2 (B), SW76.2 (B), U1.13 (S11)
COL12: SW13.2 (B), SW27.2 (B), SW41.2 (B), SW55.2 (B), U1.14 (S12)
COL13: SW14.2 (B), SW28.2 (B), SW42.2 (B), U1.15 (S13)
GND: D15.1 (K), D16.1 (K), J1.7, J2.7, U1.12 (GND), U1.18 (E0), U1.19 (E1), U2.10 (VSS), U2.15 (A0), U2.16 (A1), U2.17 (A2)
LED0: R2.2, U2.8 (GPB7)
LED1: R3.2, U2.28 (GPA7)
unnamed: D1.1 (K), SW1.1 (A)
unnamed: D2.1 (K), SW2.1 (A)
unnamed: D3.1 (K), SW3.1 (A)
unnamed: D4.1 (K), SW4.1 (A)
unnamed: D5.1 (K), SW5.1 (A)
unnamed: D6.1 (K), SW6.1 (A)
unnamed: D7.1 (K), SW7.1 (A)
unnamed: D8.1 (K), SW8.1 (A)
unnamed: D9.1 (K), SW9.1 (A)
unnamed: D10.1 (K), SW10.1 (A)
unnamed: D11.1 (K), SW11.1 (A)
unnamed: D12.1 (K), SW12.1 (A)
unnamed: D13.1 (K), SW13.1 (A)
unnamed: D14.1 (K), SW14.1 (A)
unnamed: D15.2 (A), R2.1
unnamed: D16.2 (A), R3.1
unnamed: D17.1 (K), SW15.1 (A)
unnamed: D18.1 (K), SW16.1 (A)
unnamed: D19.1 (K), SW17.1 (A)
unnamed: D20.1 (K), SW18.1 (A)
unnamed: D21.1 (K), SW19.1 (A)
unnamed: D22.1 (K), SW20.1 (A)
unnamed: D23.1 (K), SW21.1 (A)
unnamed: D24.1 (K), SW22.1 (A)
unnamed: D25.1 (K), SW23.1 (A)
unnamed: D26.1 (K), SW24.1 (A)
unnamed: D27.1 (K), SW25.1 (A)
unnamed: D28.1 (K), SW26.1 (A)
unnamed: D29.1 (K), SW27.1 (A)
unnamed: D30.1 (K), SW28.1 (A)
unnamed: D31.1 (K), SW29.1 (A)
unnamed: D32.1 (K), SW30.1 (A)
unnamed: D33.1 (K), SW31.1 (A)
unnamed: D34.1 (K), SW32.1 (A)
unnamed: D35.1 (K), SW33.1 (A)
unnamed: D36.1 (K), SW34.1 (A)
unnamed: D37.1 (K), SW35.1 (A)
unnamed: D38.1 (K), SW36.1 (A)
unnamed: D39.1 (K), SW37.1 (A)
unnamed: D40.1 (K), SW38.1 (A)
unnamed: D41.1 (K), SW39.1 (A)
unnamed: D42.1 (K), SW40.1 (A)
unnamed: D43.1 (K), SW41.1 (A)
unnamed: D44.1 (K), SW42.1 (A)
unnamed: D45.1 (K), SW43.1 (A)
unnamed: D46.1 (K), SW44.1 (A)
unnamed: D47.1 (K), SW45.1 (A)
unnamed: D48.1 (K), SW46.1 (A)
unnamed: D49.1 (K), SW47.1 (A)
unnamed: D50.1 (K), SW48.1 (A)
unnamed: D51.1 (K), SW49.1 (A)
unnamed: D52.1 (K), SW50.1 (A)
unnamed: D53.1 (K), SW51.1 (A)
unnamed: D54.1 (K), SW52.1 (A)
unnamed: D55.1 (K), SW53.1 (A)
unnamed: D56.1 (K), SW54.1 (A)
unnamed: D57.1 (K), SW55.1 (A)
unnamed: D58.1 (K), SW56.1 (A)
unnamed: D59.1 (K), SW57.1 (A)
unnamed: D60.1 (K), SW58.1 (A)
unnamed: D61.1 (K), SW59.1 (A)
unnamed: D62.1 (K), SW60.1 (A)
unnamed: D63.1 (K), SW61.1 (A)
unnamed: D64.1 (K), SW62.1 (A)
unnamed: D65.1 (K), SW63.1 (A)
unnamed: D66.1 (K), SW64.1 (A)
unnamed: D67.1 (K), SW65.1 (A)
unnamed: D68.1 (K), SW66.1 (A)
unnamed: D69.1 (K), SW67.1 (A)
unnamed: D70.1 (K), SW68.1 (A)
unnamed: D71.1 (K), SW69.1 (A)
unnamed: D72.1 (K), SW70.1 (A)
unnamed: D73.1 (K), SW71.1 (A)
unnamed: D74.1 (K), SW72.1 (A)
unnamed: D75.1 (K), SW73.1 (A)
unnamed: D76.1 (K), SW74.1 (A)
unnamed: D77.1 (K), SW75.1 (A)
unnamed: D78.1 (K), SW76.1 (A)
unnamed: D79.1 (K), SW77.1 (A)
unnamed: D80.1 (K), SW78.1 (A)
unnamed: D81.1 (K), SW79.1 (A)
unnamed: D82.1 (K), SW80.1 (A)
unnamed: D83.1 (K), SW81.1 (A)
unnamed: D84.1 (K), SW82.1 (A)
unnamed: D85.1 (K), SW83.1 (A)
unnamed: D86.1 (K), SW84.1 (A)
unnamed: D87.1 (K), SW85.1 (A)
unnamed: D88.1 (K), SW86.1 (A)
unnamed: D89.1 (K), SW87.1 (A)
unnamed: D90.1 (K), SW88.1 (A)
unnamed: D91.1 (K), SW89.1 (A)
unnamed: D92.1 (K), SW90.1 (A)
unnamed: D93.1 (K), SW91.1 (A)
unnamed: D94.1 (K), SW92.1 (A)
unnamed: D95.1 (K), SW93.1 (A)
unnamed: D96.1 (K), SW94.1 (A)
unnamed: D97.1 (K), SW95.1 (A)
unnamed: D98.1 (K), SW96.1 (A)
unnamed: D99.1 (K), SW97.1 (A)
unnamed: D100.1 (K), SW98.1 (A)
unnamed: D101.1 (K), SW99.1 (A)
unnamed: D102.1 (K), SW100.1 (A)
unnamed: R7.2, U2.18 (~RESET)
unnamed: U1.20 (A3), U2.4 (GPB3)
unnamed: U1.21 (A2), U2.3 (GPB2)
unnamed: U1.22 (A1), U2.2 (GPB1)
unnamed: U1.23 (A0), U2.1 (GPB0)
ROW0: D1.2 (A), D2.2 (A), D3.2 (A), D4.2 (A), D5.2 (A), D6.2 (A), D7.2 (A), D8.2 (A), D9.2 (A), D10.2 (A), D11.2 (A), D12.2 (A), D13.2 (A), D14.2 (A), U2.5 (GPB4)
ROW1: D17.2 (A), D18.2 (A), D19.2 (A), D20.2 (A), D21.2 (A), D22.2 (A), D23.2 (A), D24.2 (A), D25.2 (A), D26.2 (A), D27.2 (A), D28.2 (A), D29.2 (A), D30.2 (A), U2.6 (GPB5)
ROW2: D31.2 (A), D32.2 (A), D33.2 (A), D34.2 (A), D35.2 (A), D36.2 (A), D37.2 (A), D38.2 (A), D39.2 (A), D40.2 (A), D41.2 (A), D42.2 (A), D43.2 (A), D44.2 (A), U2.7 (GPB6)
ROW3: D45.2 (A), D46.2 (A), D47.2 (A), D48.2 (A), D49.2 (A), D50.2 (A), D51.2 (A), D52.2 (A), D53.2 (A), D54.2 (A), D55.2 (A), D56.2 (A), D57.2 (A), U2.21 (GPA0)
ROW4: D58.2 (A), D59.2 (A), D60.2 (A), D61.2 (A), D62.2 (A), D63.2 (A), D64.2 (A), D65.2 (A), D66.2 (A), D67.2 (A), D68.2 (A), D69.2 (A), U2.22 (GPA1)
ROW5: D70.2 (A), D71.2 (A), D72.2 (A), D73.2 (A), D74.2 (A), D75.2 (A), D76.2 (A), D77.2 (A), D78.2 (A), U2.23 (GPA2)
ROW6: D79.2 (A), D80.2 (A), D81.2 (A), D82.2 (A), D83.2 (A), D84.2 (A), D85.2 (A), U2.24 (GPA3)
ROW7: D86.2 (A), D87.2 (A), D88.2 (A), D89.2 (A), D90.2 (A), D91.2 (A), U2.25 (GPA4)
ROW8: D92.2 (A), D93.2 (A), D94.2 (A), D95.2 (A), D96.2 (A), D97.2 (A), U2.26 (GPA5)
ROW9: D98.2 (A), D99.2 (A), D100.2 (A), D101.2 (A), D102.2 (A), U2.27 (GPA6)
SCL: J1.5, J2.5, U2.12 (SCK)
SDA: J1.6, J2.6, U2.13 (SDA)
SNES_CLK: J1.2, J2.2
SNES_DATA: J1.4, J2.4
SNES_LATCH: J1.3, J2.3
VCC: J1.1, J2.1, R7.1, U1.24 (VCC), U2.9 (VDD)
