studio8502/Sentinel-65X/firmware/kernel/include/config.h

//*****************************************************************************
//  Turaco-DOS
//
//  include/config.h
//*****************************************************************************

#pragma once

#define PROJECT_NAME Sentinel 65X Kernel
#define VERSION 0.0.1
#define COPYRIGHT Copyright (c) 2024 Kyle J Cardoza
